TheJustMoose/74HCPU/hard/MUX1/MUX1.kicad_pcb

## KiCad design hard/MUX1/MUX1.kicad_pcb (2026-05-10)

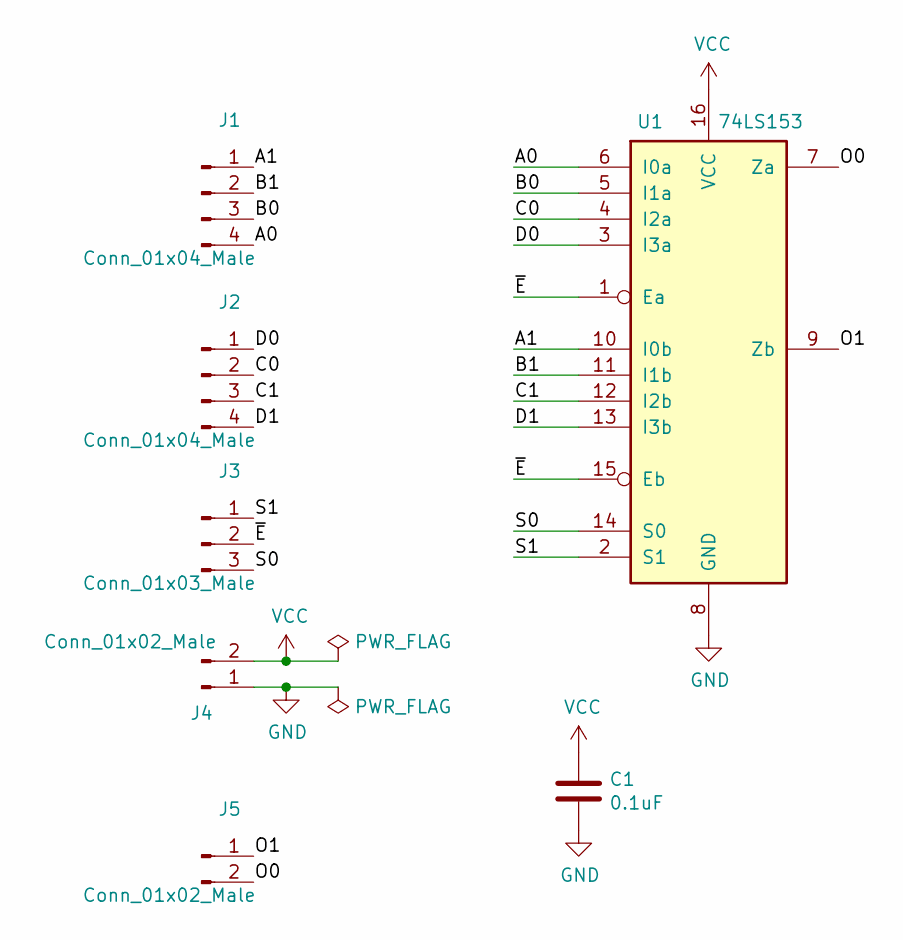
[picture p34: schematic MUX1.kicad_sch]

Parts:
C1: 0.1uF; C_0805_2012Metric_Pad1.18x1.45mm_HandSolder
J1, J2: Conn_01x04_Male; PinHeader_1x04_P2.54mm_Horizontal
J3: Conn_01x03_Male; PinHeader_1x03_P2.54mm_Horizontal
J4, J5: Conn_01x02_Male; PinHeader_1x02_P2.54mm_Horizontal
U1: 74LS153; SO-16_3.9x9.9mm_P1.27mm

Connections:
/A0: J1.4, U1.6 (I0a)
/A1: J1.1, U1.10 (I0b)
/B0: J1.3, U1.5 (I1a)
/B1: J1.2, U1.11 (I1b)
/C0: J2.2, U1.4 (I2a)
/C1: J2.3, U1.12 (I2b)
/D0: J2.1, U1.3 (I3a)
/D1: J2.4, U1.13 (I3b)
/O0: J5.2, U1.7 (Za)
/O1: J5.1, U1.9 (Zb)
/S0: J3.3, U1.14 (S0)
/S1: J3.1, U1.2 (S1)
/~E: J3.2, U1.1 (Ea), U1.15 (Eb)
GND: C1.2, J4.1, U1.8 (GND)
VCC: C1.1, J4.2, U1.16 (VCC)

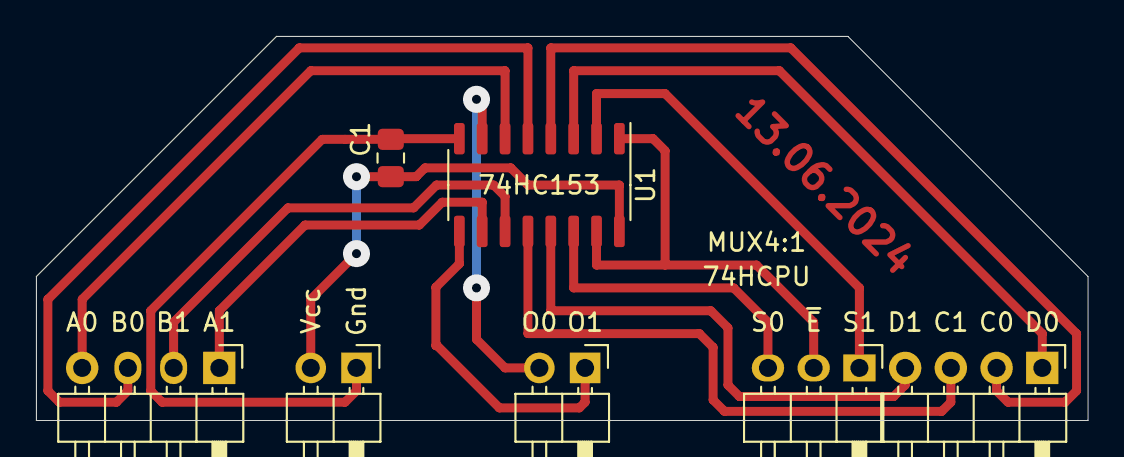
[picture p35: board MUX1.kicad_pcb from above]

Board: 2 copper layers, 58.4 x 21.3 mm, 7 parts (0 on the bottom side), 15 nets.
