TheJustMoose/74HCPU/hard/!ROM/ROM.kicad_pcb

## KiCad design hard/!ROM/ROM.kicad_pcb (2026-05-10)

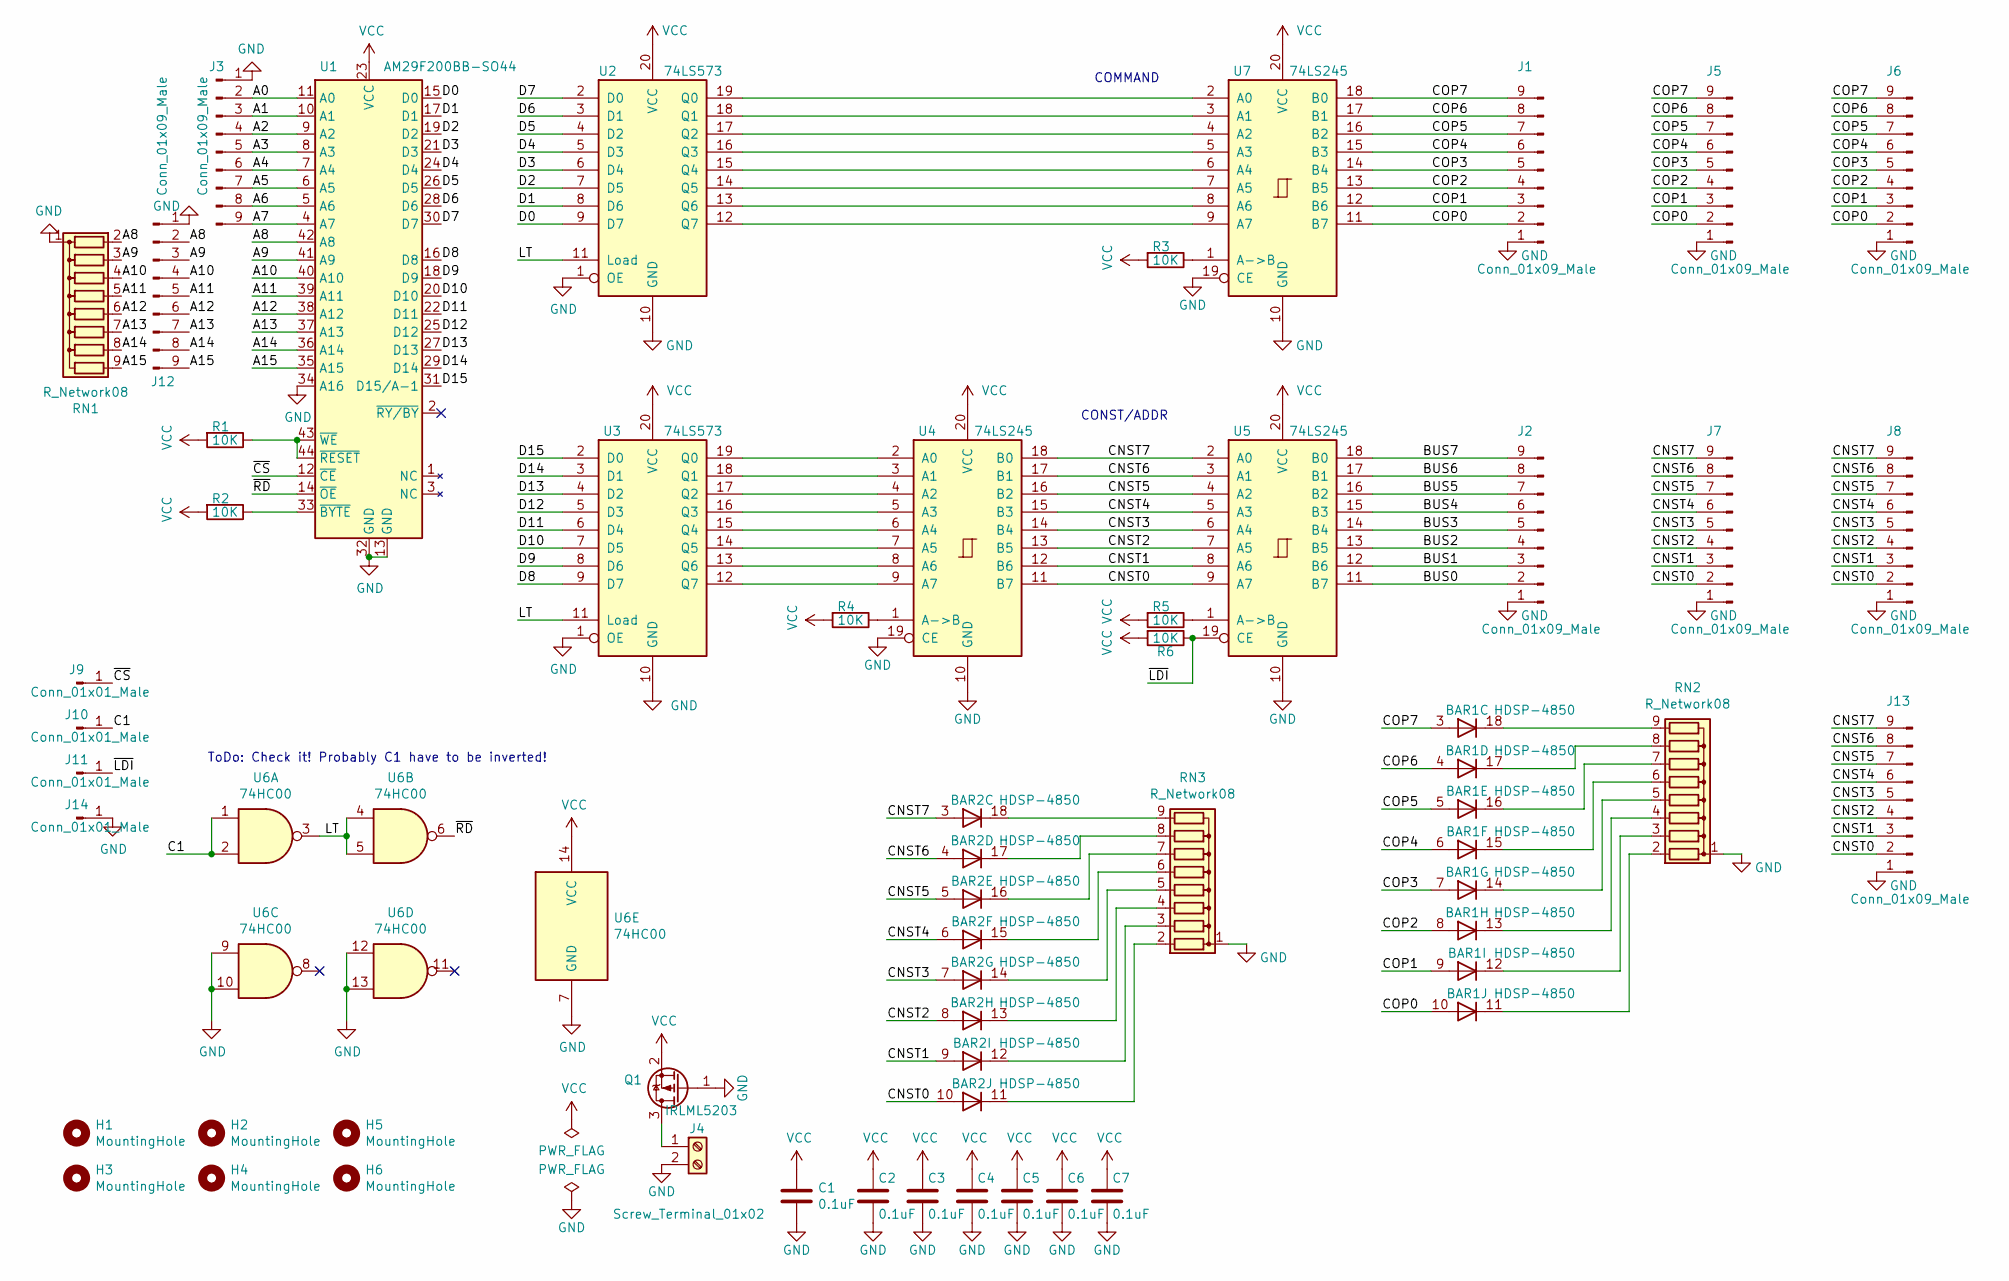
[picture p36: schematic ROM.kicad_sch]

Parts:
BAR1, BAR2: HDSP-4850
C1: 0.1uF; C_Rect_L24.0mm_W7.0mm_P22.50mm_MKT
C2, C3, C4, C5, C6, C7: 0.1uF; C_Disc_D7.5mm_W5.0mm_P7.50mm
H1, H2, H3, H4, H5, H6: MountingHole; MountingHole_3.2mm_M3
J1, J2, J3, J5, J6, J7, J8, J12, J13: Conn_01x09_Male; PinHeader_1x09_P2.54mm_Vertical
J4: Screw_Terminal_01x02; TerminalBlock_Phoenix_PT-1,5-2-5.0-H_1x02_P5.00mm_Horizontal
J9, J10, J11, J14: Conn_01x01_Male; PinHeader_1x01_P2.54mm_Vertical
Q1: IRLML5203; SOT-23
R1, R2, R3, R4, R5, R6: 10K; R_0805_2012Metric_Pad1.20x1.40mm_HandSolder
RN1, RN2, RN3: R_Network08; R_Array_SIP9
U1: AM29F200BB-SO44; DIP-44_W15.24mm
U2, U3: 74LS573; DIP-20_W7.62mm
U4, U5, U7: 74LS245; DIP-20_W7.62mm
U6: 74HC00; DIP-14_W7.62mm

Connections:
/A0: J3.2, U1.11 (A0)
/A1: J3.3, U1.10 (A1)
/A2: J3.4, U1.9 (A2)
/A3: J3.5, U1.8 (A3)
/A4: J3.6, U1.7 (A4)
/A5: J3.7, U1.6 (A5)
/A6: J3.8, U1.5 (A6)
/A7: J3.9, U1.4 (A7)
/A8: J12.2, RN1.2 (R1), U1.42 (A8)
/A9: J12.3, RN1.3 (R2), U1.41 (A9)
/A10: J12.4, RN1.4 (R3), U1.40 (A10)
/A11: J12.5, RN1.5 (R4), U1.39 (A11)
/A12: J12.6, RN1.6 (R5), U1.38 (A12)
/A13: J12.7, RN1.7 (R6), U1.37 (A13)
/A14: J12.8, RN1.8 (R7), U1.36 (A14)
/A15: J12.9, RN1.9 (R8), U1.35 (A15)
/BUS0: J2.2, U5.11 (B7)
/BUS1: J2.3, U5.12 (B6)
/BUS2: J2.4, U5.13 (B5)
/BUS3: J2.5, U5.14 (B4)
/BUS4: J2.6, U5.15 (B3)
/BUS5: J2.7, U5.16 (B2)
/BUS6: J2.8, U5.17 (B1)
/BUS7: J2.9, U5.18 (B0)
/C1: J10.1, U6.1, U6.2
/CNST0: BAR2.10 (A), J7.2, J8.2, J13.2, U4.11 (B7), U5.9 (A7)
/CNST1: BAR2.9 (A), J7.3, J8.3, J13.3, U4.12 (B6), U5.8 (A6)
/CNST2: BAR2.8 (A), J7.4, J8.4, J13.4, U4.13 (B5), U5.7 (A5)
/CNST3: BAR2.7 (A), J7.5, J8.5, J13.5, U4.14 (B4), U5.6 (A4)
/CNST4: BAR2.6 (A), J7.6, J8.6, J13.6, U4.15 (B3), U5.5 (A3)
/CNST5: BAR2.5 (A), J7.7, J8.7, J13.7, U4.16 (B2), U5.4 (A2)
/CNST6: BAR2.4 (A), J7.8, J8.8, J13.8, U4.17 (B1), U5.3 (A1)
/CNST7: BAR2.3 (A), J7.9, J8.9, J13.9, U4.18 (B0), U5.2 (A0)
/COP0: BAR1.10 (A), J1.2, J5.2, J6.2, U7.11 (B7)
/COP1: BAR1.9 (A), J1.3, J5.3, J6.3, U7.12 (B6)
/COP2: BAR1.8 (A), J1.4, J5.4, J6.4, U7.13 (B5)
/COP3: BAR1.7 (A), J1.5, J5.5, J6.5, U7.14 (B4)
/COP4: BAR1.6 (A), J1.6, J5.6, J6.6, U7.15 (B3)
/COP5: BAR1.5 (A), J1.7, J5.7, J6.7, U7.16 (B2)
/COP6: BAR1.4 (A), J1.8, J5.8, J6.8, U7.17 (B1)
/COP7: BAR1.3 (A), J1.9, J5.9, J6.9, U7.18 (B0)
/D0: U1.15 (D0), U2.9 (D7)
/D1: U1.17 (D1), U2.8 (D6)
/D2: U1.19 (D2), U2.7 (D5)
/D3: U1.21 (D3), U2.6 (D4)
/D4: U1.24 (D4), U2.5 (D3)
/D5: U1.26 (D5), U2.4 (D2)
/D6: U1.28 (D6), U2.3 (D1)
/D7: U1.30 (D7), U2.2 (D0)
/D8: U1.16 (D8), U3.9 (D7)
/D9: U1.18 (D9), U3.8 (D6)
/D10: U1.20 (D10), U3.7 (D5)
/D11: U1.22 (D11), U3.6 (D4)
/D12: U1.25 (D12), U3.5 (D3)
/D13: U1.27 (D13), U3.4 (D2)
/D14: U1.29 (D14), U3.3 (D1)
/D15: U1.31 (D15/A-1), U3.2 (D0)
/LT: U2.11 (Load), U3.11 (Load), U6.3, U6.4, U6.5
/~CS: J9.1, U1.12 (~CE)
/~LDI: J11.1, R6.1, U5.19 (CE)
/~RD: U1.14 (~OE), U6.6
GND: C1.2, C2.2, C3.2, C4.2, C5.2, C6.2, C7.2, J1.1, J2.1, J3.1, J4.2, J5.1, J6.1, J7.1, J8.1, J12.1, J13.1, J14.1, Q1.1 (G), RN1.1 (common), RN2.1 (common), RN3.1 (common), U1.13 (GND), U1.32 (GND), U1.34 (A16), U2.1 (OE), U2.10 (GND), U3.1 (OE), U3.10 (GND), U4.10 (GND), U4.19 (CE), U5.10 (GND), U6.7 (GND), U6.9, U6.10, U6.12, U6.13, U7.10 (GND), U7.19 (CE)
unnamed: BAR1.11 (K), RN2.2 (R1)
unnamed: BAR1.12 (K), RN2.3 (R2)
unnamed: BAR1.13 (K), RN2.4 (R3)
unnamed: BAR1.14 (K), RN2.5 (R4)
unnamed: BAR1.15 (K), RN2.6 (R5)
unnamed: BAR1.16 (K), RN2.7 (R6)
unnamed: BAR1.17 (K), RN2.8 (R7)
unnamed: BAR1.18 (K), RN2.9 (R8)
unnamed: BAR2.11 (K), RN3.2 (R1)
unnamed: BAR2.12 (K), RN3.3 (R2)
unnamed: BAR2.13 (K), RN3.4 (R3)
unnamed: BAR2.14 (K), RN3.5 (R4)
unnamed: BAR2.15 (K), RN3.6 (R5)
unnamed: BAR2.16 (K), RN3.7 (R6)
unnamed: BAR2.17 (K), RN3.8 (R7)
unnamed: BAR2.18 (K), RN3.9 (R8)
unnamed: J4.1, Q1.3 (D)
unnamed: R1.1, U1.43 (~WE), U1.44 (~RESET)
unnamed: R2.1, U1.33 (~BYTE)
unnamed: R3.1, U7.1 (A->B)
unnamed: R4.1, U4.1 (A->B)
unnamed: R5.1, U5.1 (A->B)
unnamed: U2.12 (Q7), U7.9 (A7)
unnamed: U2.13 (Q6), U7.8 (A6)
unnamed: U2.14 (Q5), U7.7 (A5)
unnamed: U2.15 (Q4), U7.6 (A4)
unnamed: U2.16 (Q3), U7.5 (A3)
unnamed: U2.17 (Q2), U7.4 (A2)
unnamed: U2.18 (Q1), U7.3 (A1)
unnamed: U2.19 (Q0), U7.2 (A0)
unnamed: U3.12 (Q7), U4.9 (A7)
unnamed: U3.13 (Q6), U4.8 (A6)
unnamed: U3.14 (Q5), U4.7 (A5)
unnamed: U3.15 (Q4), U4.6 (A4)
unnamed: U3.16 (Q3), U4.5 (A3)
unnamed: U3.17 (Q2), U4.4 (A2)
unnamed: U3.18 (Q1), U4.3 (A1)
unnamed: U3.19 (Q0), U4.2 (A0)
VCC: C1.1, C2.1, C3.1, C4.1, C5.1, C6.1, C7.1, Q1.2 (S), R1.2, R2.2, R3.2, R4.2, R5.2, R6.2, U1.23 (VCC), U2.20 (VCC), U3.20 (VCC), U4.20 (VCC), U5.20 (VCC), U6.14 (VCC), U7.20 (VCC)

Notes on the sheet:
CONST/ADDR
ToDo: Check it! Probably C1 have to be inverted!
COMMAND

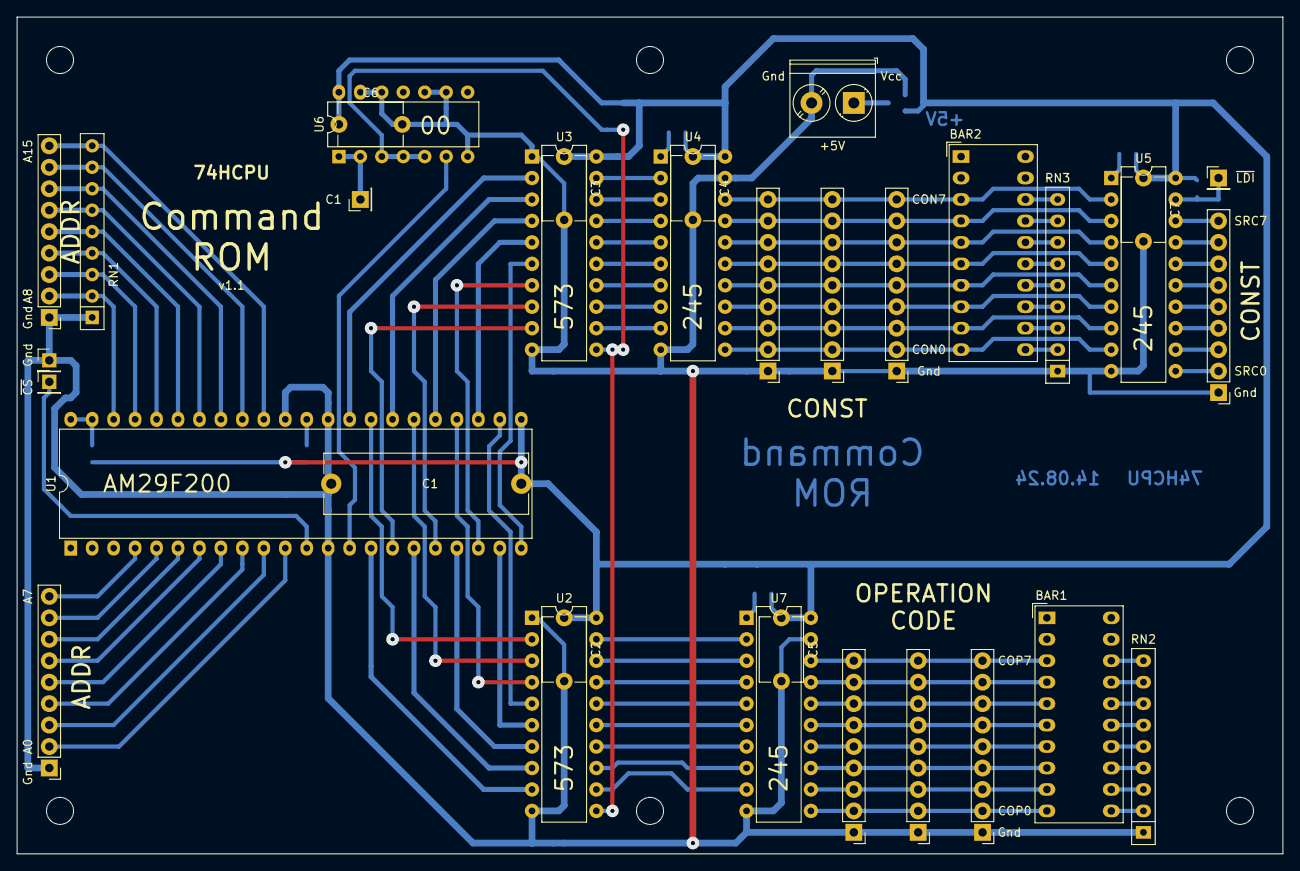
[picture p37: board ROM.kicad_pcb from above]

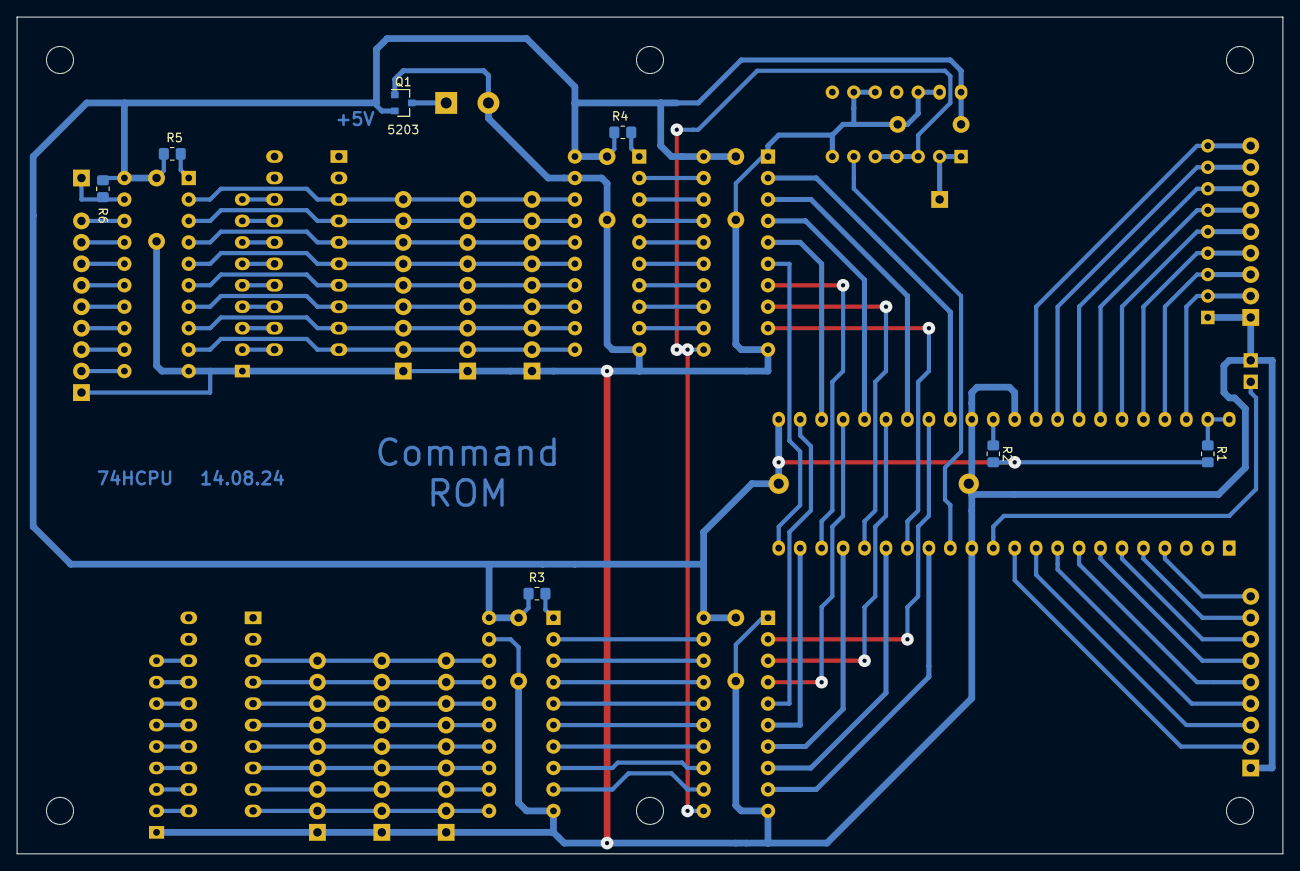
[picture p38: board ROM.kicad_pcb from below]

Board: 2 copper layers, 149.9 x 99.1 mm, 46 parts (7 on the bottom side), 101 nets.
