TheJustMoose/74HCPU/hard/!REGS/EndPlate/EndPlate.kicad_pcb

## KiCad design hard/!REGS/EndPlate/EndPlate.kicad_pcb (2026-05-01)

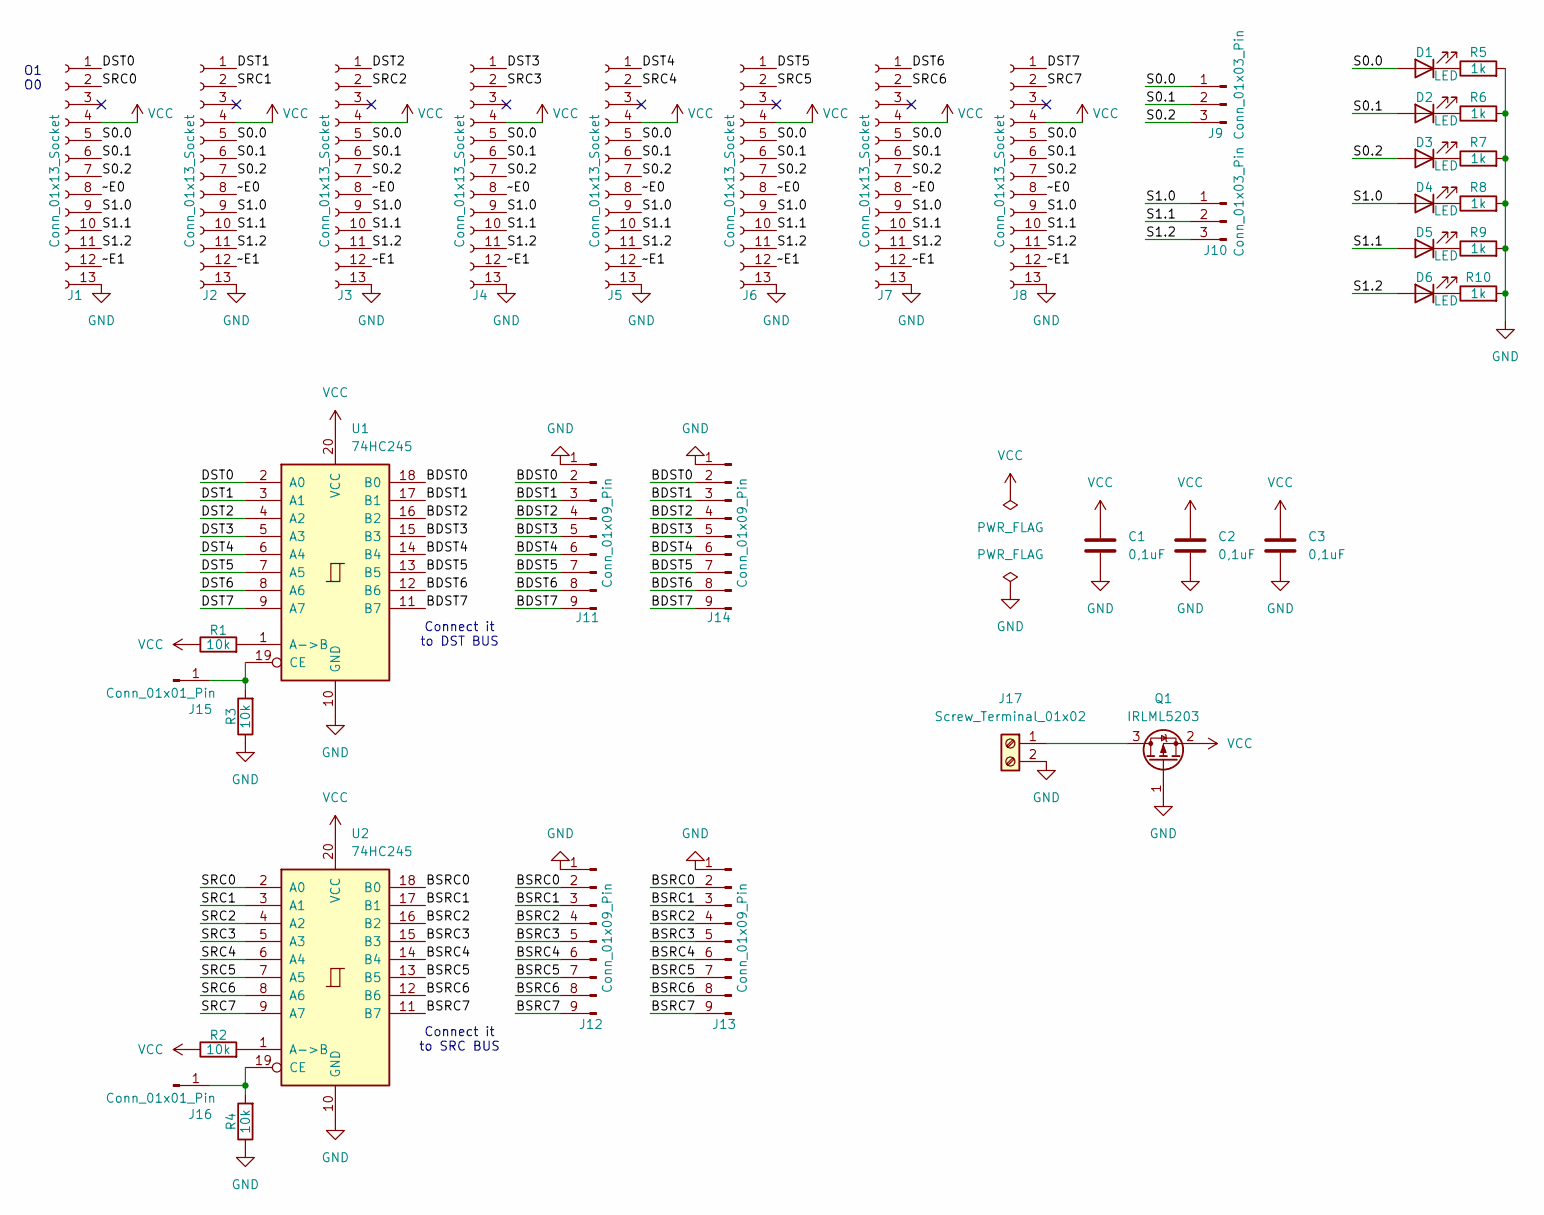
[picture p39: schematic EndPlate.kicad_sch]

Parts:
C1, C2: 0,1uF; C_Axial_L12.0mm_D6.5mm_P15.00mm_Horizontal
C3: 0,1uF; C_0805_2012Metric_Pad1.18x1.45mm_HandSolder
D1, D2, D3, D4, D5, D6: LED; LED_Rectangular_W5.0mm_H2.0mm
J1, J2, J3, J4, J5, J6, J7, J8: Conn_01x13_Socket; PinSocket_1x13_P2.54mm_Vertical_SMD_Pin1Left
J9, J10: Conn_01x03_Pin; PinHeader_1x03_P2.54mm_Vertical
J11, J12, J13, J14: Conn_01x09_Pin; PinHeader_1x09_P2.54mm_Vertical
J15, J16: Conn_01x01_Pin; PinHeader_1x01_P2.54mm_Vertical
J17: Screw_Terminal_01x02; TerminalBlock_Phoenix_MKDS-1,5-2_1x02_P5.00mm_Horizontal
Q1: IRLML5203; SOT-23
R1, R2, R3, R4: 10k; R_0805_2012Metric_Pad1.20x1.40mm_HandSolder
R5, R6, R7, R8, R9, R10: 1k; R_0805_2012Metric_Pad1.20x1.40mm_HandSolder
U1, U2: 74HC245; DIP-20_W7.62mm_Socket

Connections:
/BDST0: J11.2, J14.2, U1.18 (B0)
/BDST1: J11.3, J14.3, U1.17 (B1)
/BDST2: J11.4, J14.4, U1.16 (B2)
/BDST3: J11.5, J14.5, U1.15 (B3)
/BDST4: J11.6, J14.6, U1.14 (B4)
/BDST5: J11.7, J14.7, U1.13 (B5)
/BDST6: J11.8, J14.8, U1.12 (B6)
/BDST7: J11.9, J14.9, U1.11 (B7)
/BSRC0: J12.2, J13.2, U2.18 (B0)
/BSRC1: J12.3, J13.3, U2.17 (B1)
/BSRC2: J12.4, J13.4, U2.16 (B2)
/BSRC3: J12.5, J13.5, U2.15 (B3)
/BSRC4: J12.6, J13.6, U2.14 (B4)
/BSRC5: J12.7, J13.7, U2.13 (B5)
/BSRC6: J12.8, J13.8, U2.12 (B6)
/BSRC7: J12.9, J13.9, U2.11 (B7)
/DST0: J1.1, U1.2 (A0)
/DST1: J2.1, U1.3 (A1)
/DST2: J3.1, U1.4 (A2)
/DST3: J4.1, U1.5 (A3)
/DST4: J5.1, U1.6 (A4)
/DST5: J6.1, U1.7 (A5)
/DST6: J7.1, U1.8 (A6)
/DST7: J8.1, U1.9 (A7)
/S0.0: D1.2 (A), J1.5, J2.5, J3.5, J4.5, J5.5, J6.5, J7.5, J8.5, J9.1
/S0.1: D2.2 (A), J1.6, J2.6, J3.6, J4.6, J5.6, J6.6, J7.6, J8.6, J9.2
/S0.2: D3.2 (A), J1.7, J2.7, J3.7, J4.7, J5.7, J6.7, J7.7, J8.7, J9.3
/S1.0: D4.2 (A), J1.9, J2.9, J3.9, J4.9, J5.9, J6.9, J7.9, J8.9, J10.1
/S1.1: D5.2 (A), J1.10, J2.10, J3.10, J4.10, J5.10, J6.10, J7.10, J8.10, J10.2
/S1.2: D6.2 (A), J1.11, J2.11, J3.11, J4.11, J5.11, J6.11, J7.11, J8.11, J10.3
/SRC0: J1.2, U2.2 (A0)
/SRC1: J2.2, U2.3 (A1)
/SRC2: J3.2, U2.4 (A2)
/SRC3: J4.2, U2.5 (A3)
/SRC4: J5.2, U2.6 (A4)
/SRC5: J6.2, U2.7 (A5)
/SRC6: J7.2, U2.8 (A6)
/SRC7: J8.2, U2.9 (A7)
/~E0: J1.8, J2.8, J3.8, J4.8, J5.8, J6.8, J7.8, J8.8
/~E1: J1.12, J2.12, J3.12, J4.12, J5.12, J6.12, J7.12, J8.12
GND: C1.2, C2.2, C3.2, J1.13, J2.13, J3.13, J4.13, J5.13, J6.13, J7.13, J8.13, J11.1, J12.1, J13.1, J14.1, J17.2, Q1.1 (G), R3.1, R4.1, R5.2, R6.2, R7.2, R8.2, R9.2, R10.2, U1.10 (GND), U2.10 (GND)
unnamed: D1.1 (K), R5.1
unnamed: D2.1 (K), R6.1
unnamed: D3.1 (K), R7.1
unnamed: D4.1 (K), R8.1
unnamed: D5.1 (K), R9.1
unnamed: D6.1 (K), R10.1
unnamed: J15.1, R3.2, U1.19 (CE)
unnamed: J16.1, R4.2, U2.19 (CE)
unnamed: J17.1, Q1.3 (D)
unnamed: R1.2, U1.1 (A->B)
unnamed: R2.2, U2.1 (A->B)
VCC: C1.1, C2.1, C3.1, J1.4, J2.4, J3.4, J4.4, J5.4, J6.4, J7.4, J8.4, Q1.2 (S), R1.1, R2.1, U1.20 (VCC), U2.20 (VCC)

Notes on the sheet:
Connect it to DST BUS
Connect it to SRC BUS
O1 O0

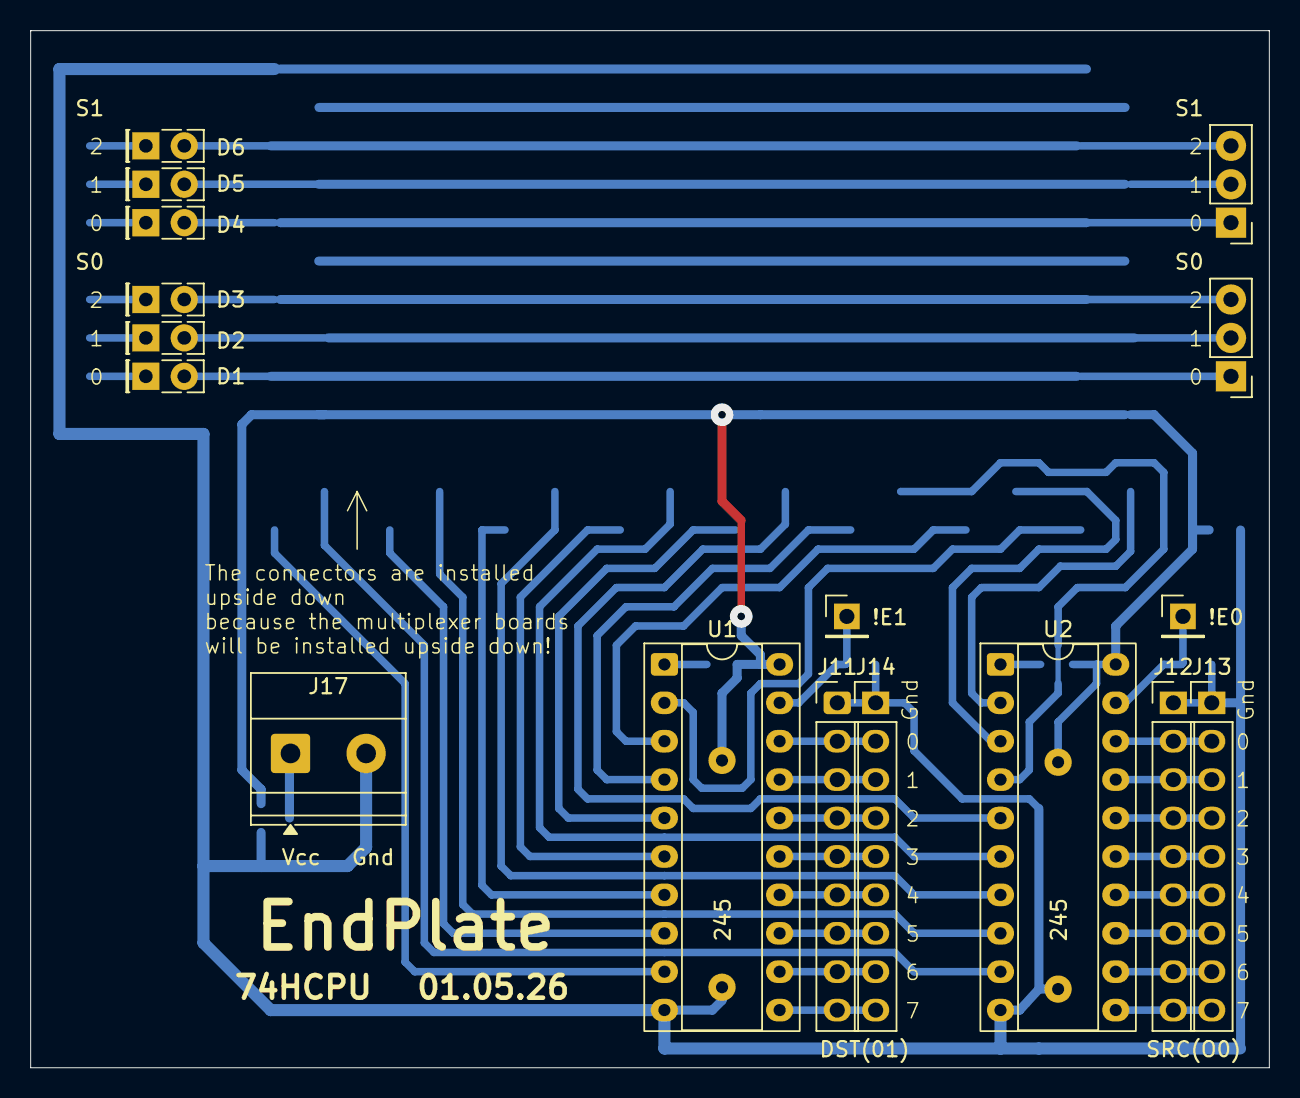
[picture p40: board EndPlate.kicad_pcb from above]

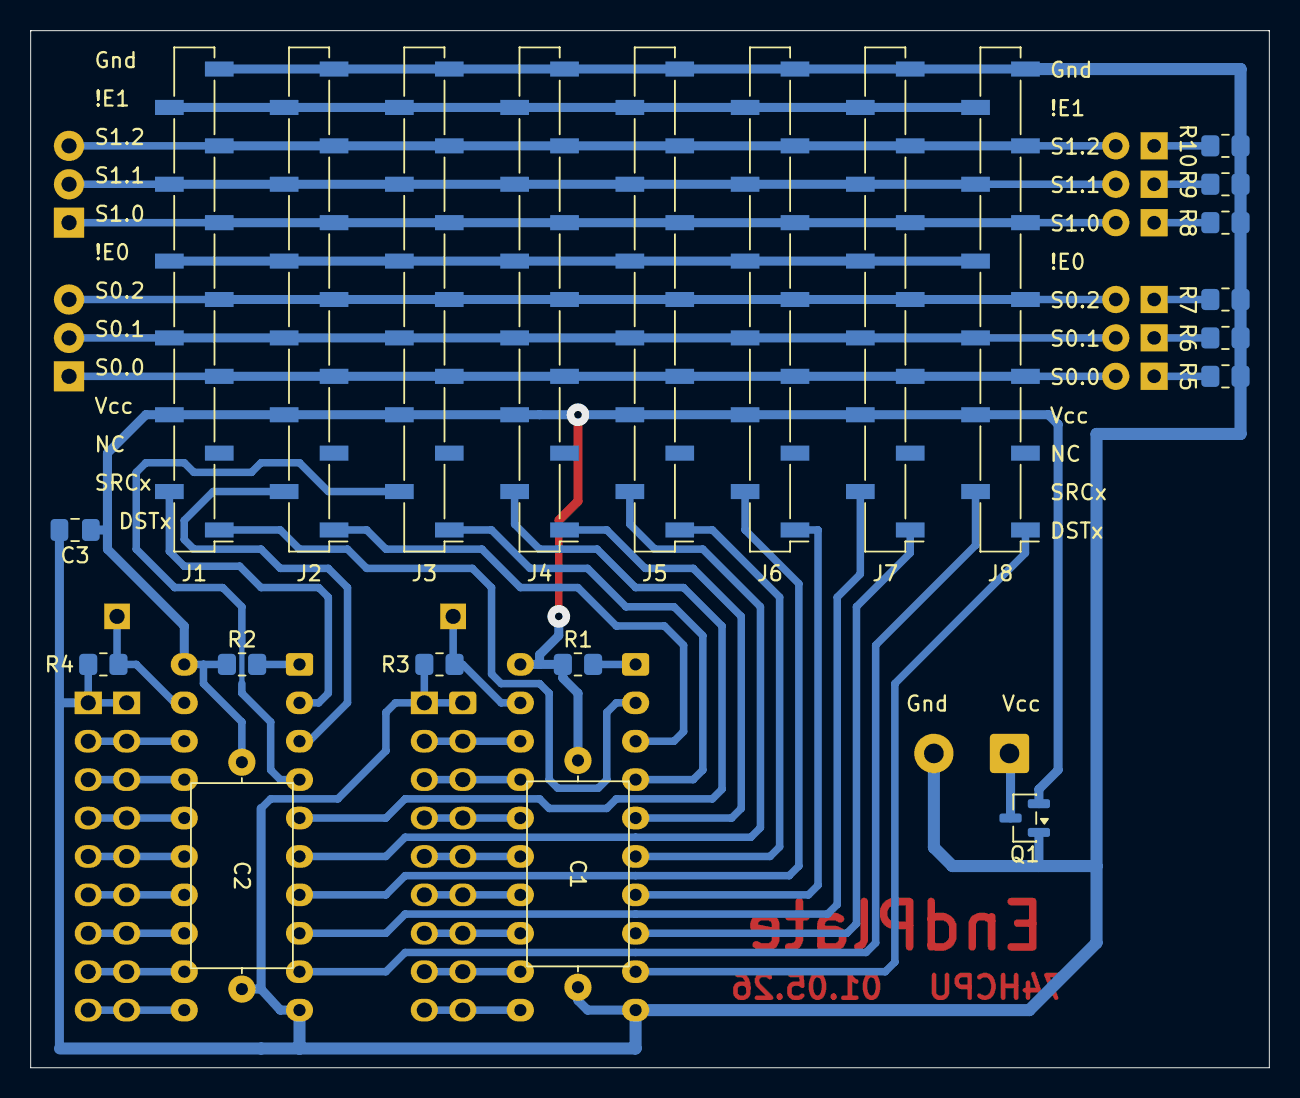
[picture p41: board EndPlate.kicad_pcb from below]

Board: 2 copper layers, 81.9 x 68.6 mm, 39 parts (22 on the bottom side), 53 nets.
