TheJustMoose/74HCPU/hard/!REGS/Regs-v5/Regs-v5.kicad_pcb

## KiCad design hard/!REGS/Regs-v5/Regs-v5.kicad_pcb (2026-03-27, an earlier design)

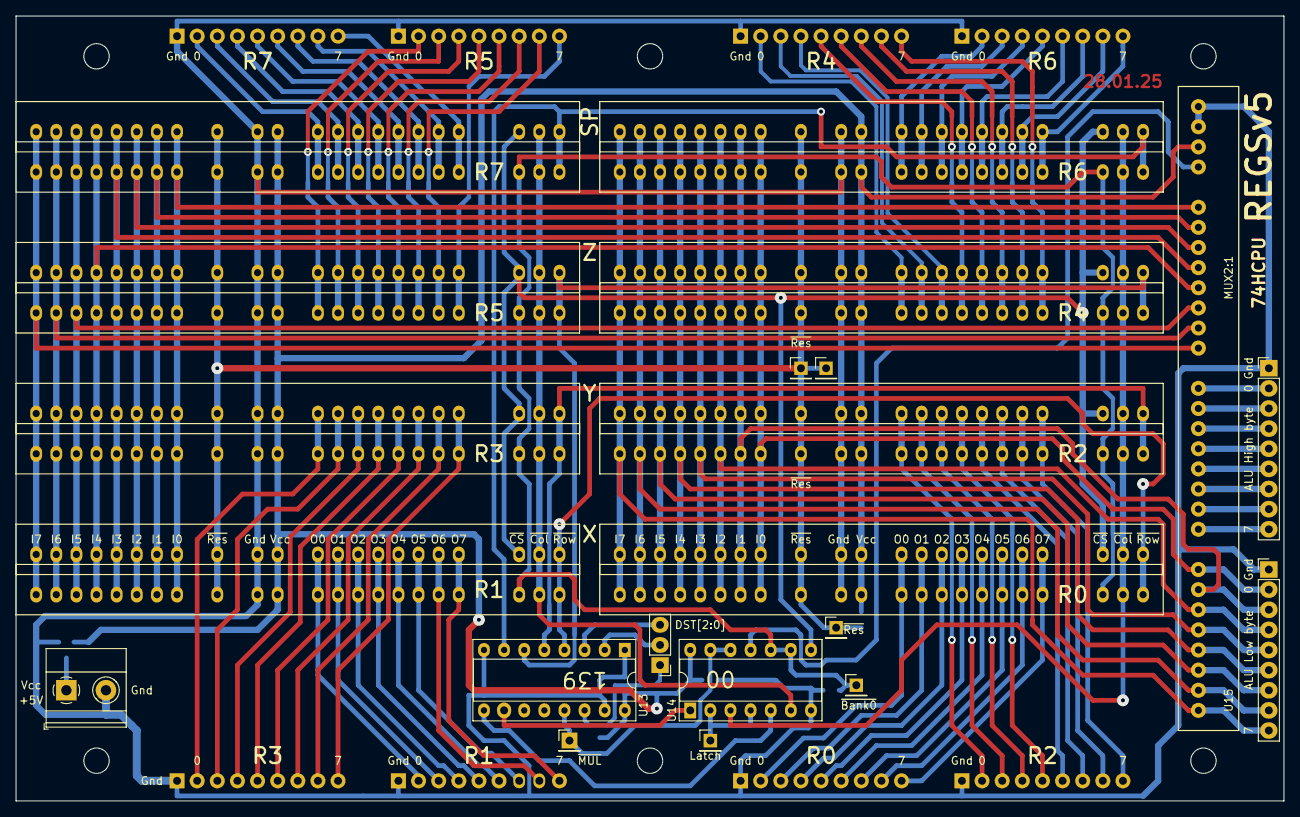
[picture p49: board Regs-v5.kicad_pcb from above]

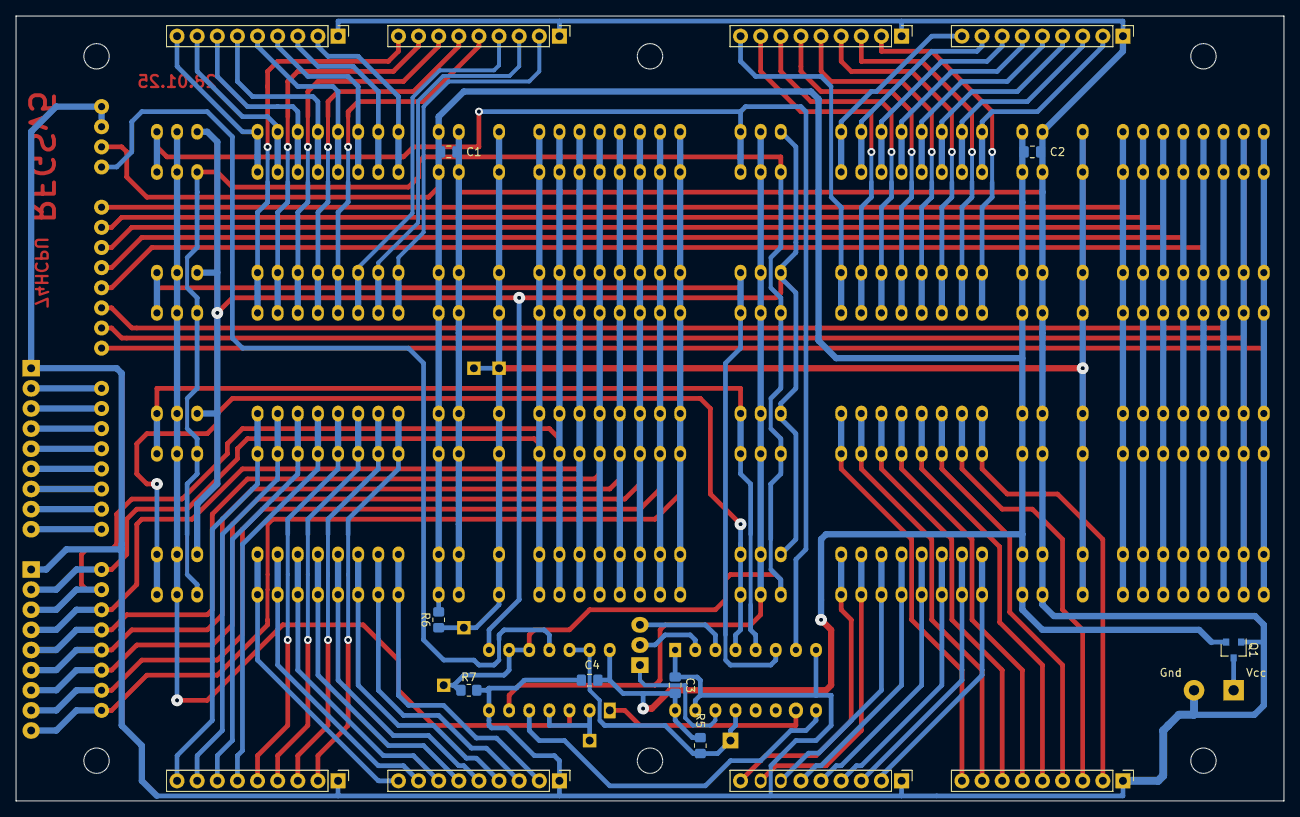
[picture p50: board Regs-v5.kicad_pcb from below]

Board: 2 copper layers, 160.0 x 99.1 mm, 51 parts (16 on the bottom side), 108 nets.

Parts:
C1, C2, C3, C4: 0.1uF; C_0805_2012Metric_Pad1.18x1.45mm_HandSolder
H1, H2, H3, H4, H5, H6: MountingHole; MountingHole_3.2mm_M3
J1, J2, J3, J4, J5, J6, J7, J8, J17, J18: Conn_01x09_Male; PinHeader_1x09_P2.54mm_Vertical
J11: Conn_01x03_Male; PinHeader_1x03_P2.54mm_Vertical
J12, J13, J14, J15, J19, J20: Conn_01x01_Male; PinHeader_1x01_P2.54mm_Vertical
J16: Screw_Terminal_01x02; TerminalBlock_Phoenix_MKDS-1,5-2_1x02_P5.00mm_Horizontal
Q1: IRLML5203; SOT-23
R5, R6, R7: 10k; R_0805_2012Metric_Pad1.20x1.40mm_HandSolder
U1, U2, U3, U4, U5, U6, U7, U8, U9, U10, U11, U12, U16, U17, U18, U19: REG_CNT
U13: 74LS139; DIP-16_W7.62mm_Socket
U14: 74HC00; DIP-14_W7.62mm_Socket
U15: MUX2-1; CMDwoC

Connections:
/ALU_H0: J18.2, U15.16
/ALU_H7: J18.9, U15.9
/DST[0]: J11.1, U13.14
/DST[1]: J11.2, U13.2
/DST[2]: J11.3, U13.3
/H0: U2.8, U4.8, U6.8, U8.8, U10.8, U12.8, U15.24, U17.8, U19.8
/H1: U2.7, U4.7, U6.7, U8.7, U10.7, U12.7, U15.23, U17.7, U19.7
/H2: U2.6, U4.6, U6.6, U8.6, U10.6, U12.6, U15.22, U17.6, U19.6
/H3: U2.5, U4.5, U6.5, U8.5, U10.5, U12.5, U15.21, U17.5, U19.5
/H4: U2.4, U4.4, U6.4, U8.4, U10.4, U12.4, U15.20, U17.4, U19.4
/H5: U2.3, U4.3, U6.3, U8.3, U10.3, U12.3, U15.19, U17.3, U19.3
/H6: U2.2, U4.2, U6.2, U8.2, U10.2, U12.2, U15.18, U17.2, U19.2
/H7: U2.1, U4.1, U6.1, U8.1, U10.1, U12.1, U15.17, U17.1, U19.1
/L0: J17.2, U1.8, U3.8, U5.8, U7.8, U9.8, U11.8, U15.8, U16.8, U18.8
/L1: J17.3, U1.7, U3.7, U5.7, U7.7, U9.7, U11.7, U15.7, U16.7, U18.7
/L2: J17.4, U1.6, U3.6, U5.6, U7.6, U9.6, U11.6, U15.6, U16.6, U18.6
/L3: J17.5, U1.5, U3.5, U5.5, U7.5, U9.5, U11.5, U15.5, U16.5, U18.5
/L4: J17.6, U1.4, U3.4, U5.4, U7.4, U9.4, U11.4, U15.4, U16.4, U18.4
/L5: J17.7, U1.3, U3.3, U5.3, U7.3, U9.3, U11.3, U15.3, U16.3, U18.3
/L6: J17.8, U1.2, U3.2, U5.2, U7.2, U9.2, U11.2, U15.2, U16.2, U18.2
/L7: J17.9, U1.1, U3.1, U5.1, U7.1, U9.1, U11.1, U15.1, U16.1, U18.1
/Latch: J15.1, U14.2, U14.4
/R0.0: J1.2, U1.12, U9.12
/R0.1: J1.3, U1.13, U9.13
/R0.2: J1.4, U1.14, U9.14
/R0.3: J1.5, U1.15, U9.15
/R0.4: J1.6, U1.16, U9.16
/R0.5: J1.7, U1.17, U9.17
/R0.6: J1.8, U1.18, U9.18
/R0.7: J1.9, U1.19, U9.19
/R1.0: J2.2, U2.12, U10.12
/R1.1: J2.3, U2.13, U10.13
/R1.2: J2.4, U2.14, U10.14
/R1.3: J2.5, U2.15, U10.15
/R1.4: J2.6, U2.16, U10.16
/R1.5: J2.7, U2.17, U10.17
/R1.6: J2.8, U2.18, U10.18
/R1.7: J2.9, U2.19, U10.19
/R2.0: J3.2, U3.12, U11.12
/R2.1: J3.3, U3.13, U11.13
/R2.2: J3.4, U3.14, U11.14
/R2.3: J3.5, U3.15, U11.15
/R2.4: J3.6, U3.16, U11.16
/R2.5: J3.7, U3.17, U11.17
/R2.6: J3.8, U3.18, U11.18
/R2.7: J3.9, U3.19, U11.19
/R3.0: J4.2, U4.12, U12.12
/R3.1: J4.3, U4.13, U12.13
/R3.2: J4.4, U4.14, U12.14
/R3.3: J4.5, U4.15, U12.15
/R3.4: J4.6, U4.16, U12.16
/R3.5: J4.7, U4.17, U12.17
/R3.6: J4.8, U4.18, U12.18
/R3.7: J4.9, U4.19, U12.19
/R4.0: J5.2, U5.12, U16.12
/R4.1: J5.3, U5.13, U16.13
/R4.2: J5.4, U5.14, U16.14
/R4.3: J5.5, U5.15, U16.15
/R4.4: J5.6, U5.16, U16.16
/R4.5: J5.7, U5.17, U16.17
/R4.6: J5.8, U5.18, U16.18
/R4.7: J5.9, U5.19, U16.19
/R5.0: J6.2, U6.12, U17.12
/R5.1: J6.3, U6.13, U17.13
/R5.2: J6.4, U6.14, U17.14
/R5.3: J6.5, U6.15, U17.15
/R5.4: J6.6, U6.16, U17.16
/R5.5: J6.7, U6.17, U17.17
/R5.6: J6.8, U6.18, U17.18
/R5.7: J6.9, U6.19, U17.19
/R6.0: J7.2, U7.12, U18.12
/R6.1: J7.3, U7.13, U18.13
/R6.2: J7.4, U7.14, U18.14
/R6.3: J7.5, U7.15, U18.15
/R6.4: J7.6, U7.16, U18.16
/R6.5: J7.7, U7.17, U18.17
/R6.6: J7.8, U7.18, U18.18
/R6.7: J7.9, U7.19, U18.19
/R7.0: J8.2, U8.12, U19.12
/R7.1: J8.3, U8.13, U19.13
/R7.2: J8.4, U8.14, U19.14
/R7.3: J8.5, U8.15, U19.15
/R7.4: J8.6, U8.16, U19.16
/R7.5: J8.7, U8.17, U19.17
/R7.6: J8.8, U8.18, U19.18
/R7.7: J8.9, U8.19, U19.19
/~Bank0: J14.1, R7.1, U1.20, U2.20, U3.20, U4.20, U5.20, U6.20, U7.20, U8.20, U14.9, U14.10
/~Bank1: U9.20, U10.20, U11.20, U12.20, U14.8, U16.20, U17.20, U18.20, U19.20
/~H: U2.21, U4.21, U6.21, U8.21, U10.21, U12.21, U14.6, U17.21, U19.21
/~L: U1.21, U3.21, U5.21, U7.21, U9.21, U11.21, U14.3, U16.21, U18.21
/~MUL: J12.1, R5.1, U13.13, U14.12, U14.13
/~R0: U1.22, U2.22, U9.22, U10.22, U13.4
/~R1: U3.22, U4.22, U11.22, U12.22, U13.5
/~R2: U5.22, U6.22, U13.6, U16.22, U17.22
/~R3: U7.22, U8.22, U13.7, U18.22, U19.22
/~Res: J13.1, J19.1, J20.1, R6.1, U1.9, U2.9, U3.9, U4.9, U5.9, U6.9, U7.9, U8.9, U9.9, U10.9, U11.9, U12.9, U16.9, U17.9, U18.9, U19.9
GND: C1.2, C2.2, C3.2, C4.2, J1.1, J2.1, J3.1, J4.1, J5.1, J6.1, J7.1, J8.1, J16.2, J17.1, J18.1, Q1.1, R7.2, U1.10, U2.10, U3.10, U4.10, U5.10, U6.10, U7.10, U8.10, U9.10, U10.10, U11.10, U12.10, U13.1, U13.8, U13.15, U14.7, U15.27, U15.28, U16.10, U17.10, U18.10, U19.10
unnamed: J16.1, Q1.3
unnamed: J18.3, U15.15
unnamed: J18.4, U15.14
unnamed: J18.5, U15.13
unnamed: J18.6, U15.12
unnamed: J18.7, U15.11
unnamed: J18.8, U15.10
unnamed: U13.9, U14.5
unnamed: U13.10, U14.1
unnamed: U14.11, U15.25
VCC: C1.1, C2.1, C3.1, C4.1, Q1.2, R5.2, R6.2, U1.11, U2.11, U3.11, U4.11, U5.11, U6.11, U7.11, U8.11, U9.11, U10.11, U11.11, U12.11, U13.16, U14.14, U15.26, U16.11, U17.11, U18.11, U19.11
