TheJustMoose/74HCPU/soft/expr/backend.cc

#include "backend.h"
#include "var_list.h"
#include "parser.h"
#include "regs_bank.h"
#include "spillable.h"
#include "var.h"
#include "var_list.h"
#include "var_size.h"

#include <algorithm>
#include <iostream>
#include <string>
#include <sstream>

using namespace std;

/*

 Добавить юнит тестов для уже написанных Spill / Fill.
 Сделать какой-то синглтон, из которого торчат переменные, адреса, и степень их заспиленности!
 Как-то переделать табличку со списком Operation

*/

// copied from asm
string ToUpper(string s) {
  transform(s.begin(), s.end(), s.begin(), ::toupper);
  return s;
}

string AlignNumber(string s, int width) {
  string res {s};
  while (res.size() < width)
    res = "0" + res;
  return res;
}

string AlignByWidth(string s, int width, char c = ' ') {
  string res {s};
  string fll({c});
  while (res.size() < width)
    res += fll;
  return res;
}

string ToHexString(int value, int width = 4) {
  stringstream ss;
  ss << hex << value;
  return AlignNumber(ToUpper(ss.str()), width);
}

class RegSpillable: public ISpillable {
 public:
  RegSpillable(Backend* backend, map<string, uint16_t> var_addrs)
    : backend_(backend), var_addrs_(var_addrs) {}

  void Spill(size_t reg_idx, uint16_t var_addr,
             string var_name) override;

  void Fill(string var_name, string reg_name) override;

 private:
  Backend* backend_ {nullptr};
  map<string, uint16_t> var_addrs_;
};

void RegSpillable::Spill(size_t reg_idx, uint16_t var_addr,
                         string var_name) {
  cout << "// No free registers. Will spill R" << reg_idx
       << " with " << var_name
       << " to addr " << var_addr << endl;

  if (!backend_) {
    cout << "backend_ is NULL" << endl;
    return;
  }

  backend_->SwitchToBank1();
  backend_->AddAsmInstruction(string("mov XL, 0x") + ToHexString(var_addr & 0xFF));
  backend_->AddAsmInstruction(string("mov XH, 0x") + ToHexString((var_addr >> 8) & 0xFF));
  backend_->SwitchToBank0();
  backend_->AddAsmInstruction(string("st X, R") + to_string(reg_idx), var_name);
}

void RegSpillable::Fill(string var_name, string reg_name) {
  // Okay, we already know that var_name was spilled early...
  if (var_addrs_.find(var_name) == var_addrs_.end()) {
    cout << "Error. Address of variable " << var_name << "was not found" << endl;
    return;
  }

  uint16_t var_addr = var_addrs_[var_name];

  backend_->SwitchToBank1();
  backend_->AddAsmInstruction(string("mov XL, 0x") + ToHexString(var_addr & 0xFF));
  backend_->AddAsmInstruction(string("mov XH, 0x") + ToHexString((var_addr >> 8) & 0xFF));
  backend_->SwitchToBank0();
  backend_->AddAsmInstruction(string("ld ") + reg_name + string(", X"), var_name);
}

size_t reg_cnt = 8;
vector<string> bank1(reg_cnt);

string FindPtrFor(string var_name) {
  // check existing pair ptr:reg
  if (bank1[0] == var_name)
    return "X";
  if (bank1[2] == var_name)
    return "Y";

  // try to insert new pair ptr:reg
  if (!bank1[0].size()) {
    bank1[0] = var_name;
    return "X";
  } else if (!bank1[2].size()) {
    bank1[2] = var_name;
    return "Y";
  } else {
  }

  // oops
  return "";
}

void Backend::AddAsmInstruction(string instr, string cmnt, string cmnt2) {
  string res {instr};
  if (cmnt.size()) {
    res = AlignByWidth(res, 22);
    res += "// ";
    res += AlignByWidth(cmnt, 10);
    res += cmnt2;
  }
  res_asm_.push_back(res);
}

void Backend::SwitchToBank0() {
  AddAsmInstruction("out  CPU_FLAGS, 0", "switch to bank 0");
}

void Backend::SwitchToBank1() {
  AddAsmInstruction("out  CPU_FLAGS, 0x40", "switch to bank 1");
}

void Backend::FreeTheRegisters(RegsBank0& bank0, const Operation& op) {
  size_t var_cnt = op.live_out_vars.size();  // this variables are still alive after instruction
  for (size_t i = 0; i < var_cnt; i++) {
    if (op.live_in_vars[i] && !op.live_out_vars[i]) {  // var has died
      string reg_name = idx_to_var_[i];
      size_t idx = bank0.GetIndexOfVar(reg_name);
      cout << "variable with idx == " << i
           << ", var_name: " << bank0[idx] << " has died" << endl;
      cout << "reg_name: " << reg_name << ", reg_idx: " << idx << endl;
      bank0.FreeTheRegister(idx);
      cout << bank0.DumpRegs() << endl;
    }
  }
}

void Backend::GenerateAssignment(RegsBank0& bank0, Operation op, Var& v) {
  if (v.is_ptr) {  // pointer ops
    string lval;
    string hval;
    if (op.num_pos() == npLeft) {  // pointer1 = 0x1000
      int val = std::stoi(op.left_arg);
      lval = ToHexString(val & 0xFF, 3) + "h";
      hval = ToHexString((val >> 8) & 0xFF, 3) + "h";
    } else {  // pointer1 = pointer2
      string left = FindPtrFor(op.left_arg);
      lval = left + "L";
      hval = left + "H";
    }

    string cmnt1 = op.res_arg + " = " + op.left_arg;

    string res_reg = FindPtrFor(op.res_arg);
    SwitchToBank1();
    string line1 = "mov " + res_reg + "L, " + lval;
    AddAsmInstruction(line1, cmnt1);
    string line2 = "mov " + res_reg + "H, " + hval;
    AddAsmInstruction(line2);
    SwitchToBank0();
  } else {  // ordinary regs
    string cmnt1 = op.res_arg + " = " + op.left_arg;

    string res_reg = bank0.FindRegFor(op.res_arg);
    string right_val = (op.num_pos() == npLeft) ? op.left_arg : bank0.FindRegFor(op.left_arg);
    string line1 = "mov " + res_reg + ", " + right_val;
    AddAsmInstruction(line1, cmnt1, bank0.DumpRegs());
  }
}

void Backend::GenerateInvertion(RegsBank0& bank0, Operation op) {
  string cmnt1 = op.res_arg + " = " + op.op_name + op.right_arg;
  string res_reg = bank0.FindRegFor(op.res_arg);
  if (op.num_pos() == npRight) {  // c = -3
    string line1 = "mov " + res_reg + ", " + op.op_name + op.right_arg;
    AddAsmInstruction(line1, cmnt1);
  } else {  // R0 = -R1
    // mov R0, ~R1; add R0, 1        // v1
    // xor R0, R0; addc R0, ~R1 + 1  // v2
    string line1 = "mov " + res_reg + ", ~" + bank0.FindRegFor(op.right_arg);
    AddAsmInstruction(line1, cmnt1);
    string line2 = "add " + res_reg + ", 1";
    AddAsmInstruction(line2);
  }
}

void Backend::GenerateBinOps(RegsBank0& bank0, Operation op) {
  // c = a + b   -->   c = a, c += b
  // what about var_size ?
  string cmnt1 = op.res_arg + " = " + op.left_arg;  // c = a

  string res_reg = bank0.FindRegFor(op.res_arg);
  string line1 = "mov " + res_reg + ", " + bank0.FindRegFor(op.left_arg);
  AddAsmInstruction(line1, cmnt1, bank0.DumpRegs());

  string cmnt2 = op.res_arg + " " + op.op_name + "= " + op.right_arg;  // c += b

  string cmd;
  if (op.op_name == "+")
    cmd = "add";
  else if (op.op_name == "-")
    cmd = "sub";
  else if (op.op_name == "*")
    cmd = "mul";
  else if (op.op_name == "/")
    cmd = "/ - not implemented!";
  else
    cmd = "unk";

  string right_val = (op.num_pos() == npRight) ? op.right_arg : bank0.FindRegFor(op.right_arg);
  string line2 = cmd + " " + res_reg + ", " + right_val;
  AddAsmInstruction(line2, cmnt2, bank0.DumpRegs());
}

void Backend::GenerateRelOps(RegsBank0& bank0, Operation op) {
  // c = a > b
  string cmnt1 = op.res_arg + " = " + op.left_arg + " " + op.op_name + " " + op.right_arg;

  string cmd;
  if (op.op_name == "<")
    cmd = "cmp";
  else if (op.op_name == ">")
    cmd = "cmp";
  else
    cmd = "unk";

  string left_reg = bank0.FindRegFor(op.left_arg);
  string right_val = (op.num_pos() == npRight) ? op.right_arg : bank0.FindRegFor(op.right_arg);
  string line1 = cmd + " " + left_reg + ", " + right_val;
  AddAsmInstruction(line1, cmnt1, bank0.DumpRegs());
}

void Backend::GenerateLabel(RegsBank0& bank0, Operation op) {
  string line1 = op.res_arg + ":";
  AddAsmInstruction(line1);
}

void Backend::GenerateJmp(RegsBank0& bank0, Operation op) {
  string line1 = op.res_arg + " " + op.left_arg;
  AddAsmInstruction(line1);
}

void Backend::GenerateBranch(RegsBank0& bank0, Operation op) {
  string line1 = op.res_arg + " " + op.left_arg;
  AddAsmInstruction(line1);
}

void Backend::GenerateCode(vector<Operation> code) {
  RegSpillable reg_spillable(this, var_addrs_);
  RegsBank0 bank0(&reg_spillable, var_addrs_, res_asm_);

  res_asm_.clear();

  for (Operation op : code) {
    if (op.op_type() == otBinaryArithm) {  // arithm ops (left_arg is not empty)
      GenerateBinOps(bank0, op);
    } else if (op.op_type() == otUnaryArithm) {  // assign ops (t1 = -t1)
      GenerateInvertion(bank0, op);
    } else if (op.op_type() == otRelational) {
      GenerateRelOps(bank0, op);
    } else if (op.op_type() == otAssignment) {  // empty op_name means assignment
      Var v;
      if (!getVar(op.res_arg, v)) {
        cout << "Variable " << op.res_arg << " was not declared" << endl;
        continue;
      }
      GenerateAssignment(bank0, op, v);
    } else if (op.op_type() == otLabel) {
      GenerateLabel(bank0, op);
    } else if (op.op_type() == otJmp) {
      GenerateJmp(bank0, op);
    } else if (op.op_type() == otBranch) {
      GenerateBranch(bank0, op);
    } else {
      cout << "**** FIXME! ****" << endl;
      cout << "Unknown op type: " << (int)op.op_type() << endl;
    }

    FreeTheRegisters(bank0, op);
  }
}
