TheJustMoose/74HCPU/soft/expr/compile.cpp

#include "compile.h"
#include "backend.h"
#include "func_guard.h"
#include "lexer.h"
#include "node.h"
#include "nodes.h"
#include "optimize.h"
#include "parser.h"
#include "print_tree.h"
#include "var_list.h"
#include "visitor.h"

#include <cstdint>
#include <iostream>
#include <map>
#include <memory>
#include <vector>

using namespace std;

int label_counter {0};
string new_label() {
  return to_string(label_counter++);
}

string RelationalOp2Branch(string op) {
  if (op == "<")
    return "jl";
  if (op == ">")
    return "jg";
  return "unk_br";
}

void PrintTableHeader() {
  cout << "|   res   | = |   left  |    op   |  right  |   numIn  |  optype  |" << endl;
}

void Print(const vector<Operation>& res_code) {
  PrintTableHeader();
  for (const Operation& r : res_code)
    cout << r.raw() << endl;
}

void PrintIR(const vector<Operation>& res_code) {
  for (const Operation& n : res_code) {
    uint8_t sz {0};
    if (isDeclared(n.res_arg, &sz))
      cout << n.str() << "(size: " << static_cast<int>(sz) << ")" << endl;
    else if (n.res_in_temp)
      cout << n.str() << endl;
    else
      cout << n.str() << "  // was not declared" << endl;
  }
}

void PrintLiveVars(const vector<Operation>& res_code,
                   map<size_t, string> idx_to_var) {
  PrintTableHeader();
  for (const Operation& r : res_code) {
    cout << r.raw() << endl;
    cout << r.live_vars_str(idx_to_var) << endl;
  }
}

class DataTypesSetter: public Visitor {
 public:
  void Visit(Name* nm_node) override {
    if (!nm_node)
      return;

    Var v;
    if (getVar(nm_node->name(), v))
      nm_node->init_data_type(v.data_type);
  }
};

void SetDataTypes(Node* root) {
  DataTypesSetter dts;
  root->accept(&dts);
}

class VarsCollector: public Visitor {
 public:
  void Visit(BinOp* binop_node) override {
    if (!binop_node)
      return;
    AddVar(binop_node->name(), binop_node->data_type(), false);  // is_ptr ?
  }

  void Visit(UnMinus* unop_node) override {
    if (!unop_node)
      return;
    AddVar(unop_node->name(), unop_node->data_type(), false);  // can we set is_ptr to true when argument is pointer?
  }
};

void CollectTempVars(Node* root) {
  VarsCollector vc;
  root->accept(&vc);
}

class CodeCollector: public Visitor {
 public:
  CodeCollector(vector<Operation>& a_res_code)
    : res_code(a_res_code) {}

  void Visit(AssignOp* asop_node) override {
    if (!asop_node->left) {
      cout << FuncGuard::stack_str() << "left == nullptr" << endl;
      return;
    }

    Name* name_node = dynamic_cast<Name*>(asop_node->left.get());
    if (!name_node) {
      cout << FuncGuard::stack_str() << "Error. left node is not variable (Name class)" << endl;
      return;
    }

    cout << FuncGuard::stack_str()
         << name_node->name() << " = "
         << asop_node->right->name() << endl;

    res_code.emplace_back(name_node->name(), "", asop_node->right->name(),
                          asop_node->get_num_pos(), "", otAssignment);
  }

  void Visit(BinOp* binop_node) override {
    if (!binop_node->left)
      cout << "left node is nullptr" << endl;
    else if (!binop_node->right)
      cout << "right node is nullptr" << endl;
    else {
      // Okay, let's put operation result into temp variable
      cout << FuncGuard::stack_str() << binop_node->name() << " = "
           << binop_node->left->name() << " " << binop_node->op() << " "
           << binop_node->right->name() << endl;
    }

    res_code.emplace_back(binop_node->name(), binop_node->op(), binop_node->left->name(),
                          binop_node->get_num_pos(), binop_node->right->name(), otBinaryArithm, true);
  }

  /*
      if (a > b) {
          c = 1;
      } else {
          c = 2;
      }
      d = c + 5;

      cmp a, b           // сравнить a и b
      jle L_else         // если a <= b, перейти в else
      c = 1
      goto L_end
  L_else:
      c = 2
  L_end:
      d = c + 5
  */
  void Visit(IfStatement* if_node) override {
    cout << "Visit(IfStatement*)" << endl;
    if (!if_node->then_body)
      cout << "then_body node is nullptr" << endl;
    else if (!if_node->cond)
      cout << "condition node is nullptr" << endl;
    else if (RelationalOp* rop = dynamic_cast<RelationalOp*>(if_node->cond.get())) {
        if_node->cond->accept(this);

        string end_label = "endif" + new_label();
        string then_label = "then" + new_label();
        string else_label = "else" + new_label();

        string br = RelationalOp2Branch(rop->op());
        res_code.emplace_back(br, "", then_label,
                              npNone, "", otBranch);

        res_code.emplace_back(else_label, "", "",
                              npNone, "", otLabel);
        if (if_node->else_body)
          if_node->else_body->accept(this);
        res_code.emplace_back("jmp", "", end_label,
                              npNone, "", otJmp);
        res_code.emplace_back(then_label, "", "",
                              npNone, "", otLabel);
        if (if_node->then_body)
          if_node->then_body->accept(this);
        res_code.emplace_back(end_label, "", "",
                              npNone, "", otLabel);
    } else {
        cout << "IfStatement require RelationalOp as a condition" << endl;
    }
  }

  void Visit(Name*) override {
    // name value will be used by other nodes
  }

  void Visit(Node*) override {
  }

  void Visit(RelationalOp* relop_node) {
    if (!relop_node->left)
      cout << "left node is nullptr" << endl;
    else if (!relop_node->right)
      cout << "right node is nullptr" << endl;
    else {
      res_code.emplace_back(relop_node->name(), relop_node->op(), relop_node->left->name(),
                            relop_node->get_num_pos(), relop_node->right->name(), otRelational, true);
    }
  }

  void Visit(UnMinus* unop_node) override {
    // the negative value is stored in the tree in two nodes: ntUMinus + ntNum
    cout << FuncGuard::stack_str() << unop_node->name() << " = "
         << unop_node->op() << unop_node->child->name() << " " << endl;

    res_code.emplace_back(unop_node->name(), unop_node->op(), "",
                          unop_node->get_num_pos(), unop_node->child->name(), otUnaryArithm, true);
  }

  void Visit(VarDecl* vd_node) override {
    for (string n : vd_node->names)
      if (vd_node->values.find(n) != vd_node->values.end())
        res_code.emplace_back(n, "", to_string(vd_node->values[n]), npLeft, "", otAssignment);
  }

 private:
  vector<Operation>& res_code;
};

void CollectCode(Node* root, vector<Operation>& res_code) {
  CodeCollector cc(res_code);
  root->accept(&cc);
}

int Compile(string code) {
  FuncGuard fg("compile");

  Lexer::instance().setInputString(code);

  vector<unique_ptr<Node>> statements;
  if (!program(statements))
    return 1;

  for (size_t i = 0; i < statements.size(); i++) {
    VarDecl* decl_node = dynamic_cast<VarDecl*>(statements[i].get());
    if (!decl_node)
      continue;

    for (string var_name : decl_node->names) {
      AddVar(var_name, decl_node->data_type(), decl_node->is_pointer());
      cout << GetDataTypeName(decl_node->data_type())
           << " variable \"" << var_name
           << (decl_node->is_pointer() ? "@" : "")
           << "\" has been declared" << endl;
    }
  }

  for (size_t i = 0; i < statements.size(); i++)
    SetDataTypes(statements[i].get());

  for (size_t i = 0; i < statements.size(); i++)
    CollectTempVars(statements[i].get());

  map<string, uint16_t> var_addrs;
  map<string, size_t> var_idxs;
  map<size_t, string> idx_to_var;

  cout << "decls:" << endl;
  uint16_t addr {0};
  cout << "| var | data_type | addr |" << endl;
  for (size_t i = 0; i < getVarCount(); i++) {
    Var v = getVar(i);
    cout << "| " << v.name << " | "
         << GetDataTypeName(v.data_type) << (v.is_ptr ? "@" : "")
         << " | " << addr << " | " << endl;

    var_addrs[v.name] = addr;  // var name -> var addr
    var_idxs[v.name] = i;      // index of variable inside of parser
    idx_to_var[i] = v.name;    // GetVar duplicate
    addr += v.size();
  }

  cout << "nodes:" << endl;
  vector<Operation> res_code;
  for (size_t i = 0; i < statements.size(); i++)
    if (statements[i])  // enum tree items, generate three-address code
      CollectCode(statements[i].get(), res_code);
    else
      cout << "statements[i] is null" << endl;

  cout << "res_code.size(): " << res_code.size() << endl << endl;

  for (size_t i = 0; i < statements.size(); i++)
    if (statements[i])
      PrintTree(statements[i].get());

  Print(res_code);
  cout << endl;

  cout << "try to optimize:" << endl;
  Optimize(res_code);
  cout << "res_code.size(): " << res_code.size() << endl;

  Print(res_code);

  cout << endl << "final IR:" << endl;
  PrintIR(res_code);

  cout << endl << "vars:" << endl;
  printVars();

  cout << endl << "processing live&dead vars..." << endl;
  vector<bool> live_vars(var_idxs.size(), false);
  for (int i = res_code.size() - 1; i >= 0; i--) {
    Operation& op = res_code[i];
    op.live_out_vars = live_vars;

    auto mark_var = [var_idxs, &live_vars](string name, bool mark) {
      // map<string, size_t> var_idxs;
      auto res_it = var_idxs.find(name);
      if (res_it != var_idxs.end())
        live_vars[res_it->second] = mark;
    };

    // -res, +left, +right
    mark_var(op.res_arg, false);
    mark_var(op.left_arg, true);
    mark_var(op.right_arg, true);

    op.live_in_vars = live_vars;
  }

  cout << endl << "printing live&dead vars..." << endl;
  PrintLiveVars(res_code, idx_to_var);
  cout << "finished" << endl << endl;

  Backend bcknd(var_addrs, idx_to_var);
  bcknd.GenerateCode(res_code);

  cout << endl << "final asm:" << endl;

  vector<string> res_asm = bcknd.GetResAsm();
  for (string& s : res_asm)
    cout << s << endl;

  return 0;
}
