TheJustMoose/74HCPU/soft/asm/assm.h

#pragma once

#include <bitset>
#include <cstdint>
#include <map>
#include <memory>
#include <optional>
#include <string>
#include <sstream>
#include <vector>

#include "ptr.h"
#include "../reg.h"
#include "slot_allocator.h"

// Code Of Operation
enum COP {
  cADD = 0x0000, cADDC = 0x1000,
  cAND = 0x2000, cOR = 0x3000, cXOR = 0x4000,
  cMUL = 0x5000, cUNO = 0x6000, cMOV = 0x7000,
  cLPM = 0x8000, cLPMW = 0x8100,
  cLD = 0x9000, cLDV = 0x9100,
  cIN = 0xA000, cOUT = 0xB000, cTOGL = 0xB004,
  cST = 0xC000, cSTV = 0xC100,
  cCMP = 0xD000, cCMPC = 0xE000,
  bCALL = 0xF000,
  bJMP = 0xF100,
  bRET = 0xF200,
  bRETI = 0xF300,
  bJL = 0xF400,
  bJE = 0xF500,
  bJNE = 0xF600,
  bJG = 0xF700,
  bJZ = 0xF800,
  bJNZ = 0xF900,
  bJC = 0xFA00,
  bJNC = 0xFB00,
  bJHC = 0xFC00,
  bJNHC = 0xFD00,
  bAFCALL = 0xFE00,
  bNOP = 0xFFFF,
  bSTOP = 0xFFFE,    // processor operation
  bERROR = 0x10000,  // we get some unknown name of operation
  cNO_OP = 0x20000   // just constant for "there is no operation here", for example for labels or error op names
};

const uint16_t cINV_LO = 0x0001;
const uint16_t cINV_HI = 0x0002;
const uint16_t cZERO_LO = 0x0004;
const uint16_t cZERO_HI = 0x0008;
const uint16_t cFORCE_CF = 0x0010;

enum OP_TYPE {
  tBINARY, tUNARY, tMEMORY, tIO, tBRANCH, tNO_OP
};

class Names {
 public:
  static COP CopFromName(std::string name);
  static REG RegFromName(std::string name);
  static PTR PtrFromName(std::string name, bool* inc, bool* dec);
  static int PortFromName(std::string name, std::string prefix);
};

class CodeGen {
 public:
  CodeGen(int line_number, COP cop)
   : line_number_(line_number), operation_(cop) {}
  virtual ~CodeGen() {}

  virtual uint16_t Emit() { return 0; }
  virtual void UpdateMachineCode(const std::map<std::string, uint16_t>& name_to_address) {}

  virtual std::vector<int> GetBlocks() { return {}; }
  virtual std::string cop() {
    std::stringstream s;
    s << std::bitset<16>(Emit());
    return s.str();
  }
  std::string FormattedCOP() {
    std::string res = cop();
    std::vector<int> blocks = GetBlocks();
    if (blocks.empty())
      return res;

    size_t pos {0};
    for (auto b : blocks) {
      pos += b;
      if (pos >= res.size())
        break;
      res.insert(pos, " ");
      pos++;
    }
    return res;
  }
  uint16_t Address() {
    return address_;
  }
  void SetAddress(uint16_t addr) {
    address_ = addr;
  }

  int LineNumber() {
    return line_number_;
  }

 protected:
  int line_number_ {0};
  uint16_t address_ {0};
  COP operation_ {cNO_OP};
};

class CodeLine {
 public:
  CodeLine(int line_number, std::string line_text);

  uint16_t GenerateMachineCode();
  void UpdateMachineCode(const std::map<std::string, uint16_t>& name_to_address);
  std::string FormattedCOP();

  std::vector<std::string> GetLabels() {
    return labels_;
  }

  bool HasLabels() {
    return labels_.size() > 0;
  }

  std::string GetLineText() {
    return line_text_;
  }

  std::optional<uint16_t> Address() {
    if (!code_gen_)
      return std::nullopt;
    return code_gen_->Address();
  }

  void SetAddress(uint16_t addr) {
    if (code_gen_)
      code_gen_->SetAddress(addr);
  }

  int LineNumber() {
    return line_number_;
  }

 private:
  int line_number_ {0};

  std::unique_ptr<CodeGen> code_gen_ {nullptr};

  std::vector<std::string> labels_ {};
  std::string line_text_ {};
};

class StringConst {
 public:
  StringConst() = default;
  StringConst(const std::string& str, int line_number): str_(str), line_number_(line_number) {}

  uint16_t GetSize() const;
  int LineNumber() const { return line_number_; }
  bool Address(uint16_t& address) const;
  void SetAddress(uint16_t);
  void PrintCode() const;
  void OutCode(std::vector<uint16_t>& code) const;
  std::string Str() const { return str_; }

 private:
  std::string str_ {};
  int line_number_ {0};
  std::optional<uint16_t> address_;
};

class DBConsts {
 public:
  DBConsts() = default;
  DBConsts(const std::vector<uint8_t>& data): data_(data) {}

  uint16_t GetSize() const;
  bool Address(uint16_t& address) const;
  void SetAddress(uint16_t address) { address_ = address; }
  void OutCode(std::vector<uint16_t>& code, bool verbose = false) const;

  std::string Join() const;

 private:
  std::vector<uint8_t> data_ {};
  std::optional<uint16_t> address_;
};

class DWConsts {
 public:
  struct Pair {
    std::string Name {};
    uint16_t Value {0};
  };

  DWConsts() = default;
  DWConsts(const std::vector<Pair>& data): data_(data) {}

  uint16_t GetSize() const;
  bool Address(uint16_t& address) const;
  void SetAddress(uint16_t address) { address_ = address; }
  void OutCode(std::vector<uint16_t>& code) const;

  std::string Join() const;

  void UpdateAddresses(const std::map<std::string, uint16_t>& new_addrs);

 private:
  std::vector<Pair> data_ {};
  std::optional<uint16_t> address_;
};

class Assembler {
 public:
  int Process(std::string fname, bool show_preprocess_out = false, bool verbose = false);
  int Process(std::map<int, std::string> lines, bool show_preprocess_out = false, bool verbose = false);
  void WriteBinary(std::string fname, bool strip_debug_info = false);

 protected:
  void PrintPreprocessed();
  void MergeCodeWithLabels();
  void ExtractOrgs();
  void ExtractStrings();
  void ExtractDBs();
  void ExtractDWs();

  void Pass1();  // generate machine code
  void Pass2();  // get real address of labels & string
  void Pass3();  // set real jump addresses

  void PrintCode();
  void OutCode(std::vector<uint16_t>& code, bool strip_debug_info = false);
  void OutDebugInfo(std::vector<uint16_t>& code);
  void PrintLabels();
  void PrintOrgs();
  void PrintStrings();
  void PrintDBs();
  void PrintDWs();

  template<typename T>
  void SetAddressesOf(std::map<std::string, T>& cont,
                      std::string cont_name, int max_line);

  bool IsOccupied(uint16_t addr) {
    return slot_allocator_.IsOccupied(addr);
  }

  void OccupyIt(uint16_t addr) {
    slot_allocator_.OccupyIt(addr);
  }

  bool OccupyIt(uint16_t addr, uint16_t size) {
    return slot_allocator_.OccupyIt(addr, size);
  }

  std::optional<uint16_t> GetFirstEmptyWindowWithSize(uint16_t size) {
    return slot_allocator_.GetFirstEmptyWindowWithSize(size);
  }

  uint16_t GetTotalSizeOfStringConsts() const;
  uint16_t GetTotalSizeOfDBConsts() const;
  uint16_t GetTotalSizeOfDWConsts() const;

 private:
  std::map<int, std::string> lines_ {};
  std::map<int, uint16_t> line_to_org_ {};
  std::vector<CodeLine> code_ {};
  // name_to_address_ contains labels and strings addresses:
  std::map<std::string, uint16_t> name_to_address_ {};

  SlotAllocator slot_allocator_;

  std::map<std::string, StringConst> string_consts_ {};
  std::map<std::string, DBConsts> db_consts_ {};
  std::map<std::string, DWConsts> dw_consts_ {};

  bool verbose_ {false};
};
