TheJustMoose/74HCPU/soft/expr/print_tree.cc

#include "print_tree.h"
#include "names.h"
#include "node.h"
#include "node_type.h"
#include "nodes.h"

#include <iostream>
#include <map>
#include <string>
#include <vector>

using namespace std;

const int kWidth = 80;

string dup(char c, int w) {
  string res(w, c);
  return res;
}

vector<Node*> gLinearTree;
map<const Node*, int> gNodeLevel;
map<const Node*, int> gNodeOffset;

void Tree2List(Node* n, int mid, int lvl = 0) {
  if (!n)
    return;
  gLinearTree.push_back(n);
  gNodeLevel[n] = lvl;
  gNodeOffset[n] = mid;
  //cout << "mid: " << mid << ", lvl: " << lvl << endl;

  if (BinOp* bop = dynamic_cast<BinOp*>(n)) {
    lvl++;
    int offset = kWidth / (lvl*2 + 5);
    Tree2List(bop->left.get(), mid - offset, lvl);
    Tree2List(bop->right.get(), mid + offset, lvl);
  } else if (RelationalOp* rop = dynamic_cast<RelationalOp*>(n)) {
    lvl++;
    int offset = kWidth / (lvl*2 + 5);
    Tree2List(rop->left.get(), mid - offset, lvl);
    Tree2List(rop->right.get(), mid + offset, lvl);
  } else if (AssignOp* aop = dynamic_cast<AssignOp*>(n)) {
    //cout << "assign..." << endl;
    lvl++;
    int offset = kWidth / (lvl*2 + 5);
    Tree2List(aop->left.get(), mid - offset, lvl);
    Tree2List(aop->right.get(), mid + offset, lvl);
  } else if (UnMinus* uop = dynamic_cast<UnMinus*>(n)) {
    //cout << "unary minus..." << endl;
    lvl++;
    Tree2List(uop->child.get(), mid, lvl);
  } else if (AddressOf* aof = dynamic_cast<AddressOf*>(n)) {
    lvl++;
    Tree2List(aof->child.get(), mid, lvl);
  } else if (DereferenceOp* dop = dynamic_cast<DereferenceOp*>(n)) {
    lvl++;
    Tree2List(dop->child.get(), mid, lvl);
  } else if (IncrementOp* iop = dynamic_cast<IncrementOp*>(n)) {
    lvl++;
    Tree2List(iop->child.get(), mid, lvl);
  } else if (IfStatement* ifop = dynamic_cast<IfStatement*>(n)) {
    lvl++;
    int offset = kWidth / (lvl*2 + 5);
    Tree2List(ifop->cond.get(), mid - offset, lvl);
    Tree2List(ifop->then_body.get(), mid + offset, lvl);
    Tree2List(ifop->else_body.get(), mid + offset, lvl);
  } else {
    //cout << "Node: " << GetNodeTypeName(n->node_type()) << endl;
  }
}

void TypeStringIntoTheBuffer(string& line, string word, int pos) {
  int left = pos - word.size() / 2;
  if (left < 0 || left >= line.size()) {
    cout << "Error! Word position is out of bounds!!" << endl;
    return;
  }

  for (size_t i = 0; i < word.size(); i++) {
    if (left + i >= line.size())
      break;
    line[left + i] = word[i];
  }
}

void PrintTree(Node* n) {
  if (!n)
    return;

  gLinearTree.clear();
  gNodeLevel.clear();
  gNodeOffset.clear();

  Tree2List(n, kWidth / 2);  // root node should be in a center of screen
  //cout << gLinearTree.size() << " items was stored" << endl;

  string line(kWidth, ' ');
  int last_lvl {0};
  int nodes_on_lvl {0};
  int cnt = 0;
  for (size_t i = 0; i < gLinearTree.size(); i++) {
    const Node* n = gLinearTree[i];
    int lvl = gNodeLevel[n];
    if (last_lvl != lvl) {
      cout << line << endl;

      line = string(kWidth, ' ');
      last_lvl = lvl;
      nodes_on_lvl = 1;  // we just found node on next level and node exist, so 'cnt' = 1
    } else {
      nodes_on_lvl++;
    }

    string name {"Oo"};
    if (const Name* name_node = dynamic_cast<const Name*>(n))
      name = name_node->name();

    if (const Num* num_node = dynamic_cast<const Num*>(n))
      name = to_string(num_node->value());

    if (const BinOp* binop_node = dynamic_cast<const BinOp*>(n))
      name = binop_node->name();

    if (const RelationalOp* rop_node = dynamic_cast<const RelationalOp*>(n))
      name = rop_node->name();

    if (const AssignOp* assop_node = dynamic_cast<const AssignOp*>(n))
      name = assop_node->op();

    if (const UnMinus* unminus_node = dynamic_cast<const UnMinus*>(n))
      name = unminus_node->name();

    if (const AddressOf* aof_node = dynamic_cast<const AddressOf*>(n))
      name = aof_node->name();

    if (const VarDecl* vard_node = dynamic_cast<const VarDecl*>(n))
      name = vard_node->var_names();

    if (const IfStatement* ifstmt_node = dynamic_cast<const IfStatement*>(n))
      name = ifstmt_node->name();

    TypeStringIntoTheBuffer(
        line,
        GetNodeTypeName(n->node_type()) + " (" + name + ")",  // to_string(gNodeOffset[n])
        gNodeOffset[n]);

    cnt++;
  }

  // Do not lose last iteration of loop!
  if (nodes_on_lvl > 0)
    cout << line << endl;

  cout << endl << dup('-', kWidth) << endl;
}
