TheJustMoose/74HCPU/soft/expr/lexer.cc

#include "lexer.h"
#include "names.h"

#include <cctype>
#include <iostream>
#include <map>

using namespace std;

map<string, Token> keywords {
  {"if", tIf},
  {"else", tElse},
};

// static
Lexer& Lexer::instance() {
  static Lexer lex;
  return lex;
}

void Lexer::consume() {
  findNextToken();
}

char Lexer::readChar() {
  return (idx_ < input_string_.size()) ? input_string_[idx_++] : 0;
}

void Lexer::findNextToken() {
  char c = readChar();
  if (isspace(c)) {     // if we have space, we have to skip it
    while (isspace(c))  // example: a b c
      c = readChar();
  }

  if (c == 0) {
    current_token_ = tEnd;
    return;
  }

  // Okay, now c != space
  if (isdigit(c)) {
    int value = 0;
    while (isdigit(c)) {
      int dig = c - '0';
      value = value*10 + dig;
      c = readChar();
    }
    if (c)
      idx_--;

    int_value_ = value;
    current_token_ = tNum;
    return;
  }

  if (isalpha(c) || c == '_') {
    string name;
    while (isalpha(c) || isdigit(c) || c == '_') {
      name += c;
      c = readChar();
    }
    if (c)
      idx_--;

    if (keywords.find(name) != keywords.end()) {
      current_token_ = keywords[name];
      return;
    }

    var_name_ = name;
    if (var_name_ == "int")
      current_token_ = tInt;
    else if (var_name_ == "byte")
      current_token_ = tByte;
    else if (var_name_ == "bool")
      current_token_ = tBool;
    else
      current_token_ = tName;
    return;
  }

  if (c == '+') {
    c = readChar();
    if (c == '+')
      current_token_ = tIncrement;
    else {
      current_token_ = tPlus;
      idx_--;
    }
    return;
  }

  if (c == '-') {
    c = readChar();
    if (c == '-')
      current_token_ = tDecrement;
    else {
      current_token_ = tMinus;
      idx_--;
    }
    return;
  }

  if (c == '<') {
    c = readChar();
    if (c == '=')
      current_token_ = tLessOrEqual;
    else {
      current_token_ = tLess;
      idx_--;
    }
    return;
  }

  if (c == '>') {
    c = readChar();
    if (c == '=')
      current_token_ = tGreaterOrEqual;
    else {
      current_token_ = tGreater;
      idx_--;
    }
    return;
  }

  if (c == '=') {
    c = readChar();
    if (c == '=')
      current_token_ = tEqual;
    else {
      current_token_ = tAssign;
      idx_--;
    }
    return;
  }

  if (c == '!') {
    c = readChar();
    if (c == '=')
      current_token_ = tNotEqual;
    else {
      current_token_ = tInversion;
      idx_--;
    }
    return;
  }

  switch (c) {
    case '*': current_token_ = tMul; return;
    case '/': current_token_ = tDiv; return;
    case '(': current_token_ = tLBracket; return;
    case ')': current_token_ = tRBracket; return;
    case ',': current_token_ = tComma; return;
    case ';': current_token_ = tSemicolon; return;
    case '@': current_token_ = tAtSign; return;
    case '#': current_token_ = tNumberSign; return;
    default: cout << "Lexer::findNextToken> Unknown token: "
                  << int(c) << endl; current_token_ = tError; break;
  }
}
