TheJustMoose/74HCPU/soft/expr/names.cc

#include "names.h"

#include <map>
#include <string>

using namespace std;

map<NodeType, string> NodeName {
  {ntName, "ntName"},
  {ntNum, "ntNum"},
  {ntSum, "ntSum"},
  {ntSub, "ntSub"},
  {ntMul, "ntMul"},
  {ntDiv, "ntDiv"},
  {ntUMinus, "ntUMinus"},
  {ntAssign, "ntAssign"},
  {ntAddressOf, "ntAddressOf"},
  {ntDereference, "ntDereference"},
  {ntIncrement, "ntIncrement"},
  {ntDecrement, "ntDecrement"},
  {ntLess, "ntLess"},
  {ntGreater, "ntGreater"},
  {ntLessOrEqual, "ntLessOrEqual"},
  {ntGreaterOrEqual, "ntGreaterOrEqual"},
  {ntIfStatement, "ntIfStatement"},
  {ntUnknown, "ntUnknown"},
  {ntVarDecl, "ntVarDecl"},
  {ntNull, "ntNull"},
};

map<Token, string> TokenName {
  {tPlus, "tPlus"},
  {tMinus, "tMinus"},
  {tMul, "tMul"},
  {tDiv, "tDiv"},
  {tNum, "tNum"},
  {tName, "tName"},
  {tComma, "tComma"},
  {tSemicolon, "tSemicolon"},
  {tAtSign, "tAtSign"},
  {tNumberSign, "tNumberSign"},
  {tLBracket, "tLBracket"},
  {tRBracket, "tRBracket"},
  {tAssign, "tAssign"},
  {tLess, "tLess"},
  {tGreater, "tGreater"},
  {tLessOrEqual, "tLessOrEqual"},
  {tGreaterOrEqual, "tGreaterOrEqual"},
  {tEqual, "tEqual"},
  {tNotEqual, "tNotEqual"},
  {tIncrement, "tIncrement"},
  {tDecrement, "tDecrement"},
  {tBool, "tBool"},
  {tByte, "tByte"},
  {tInt, "tInt"},
  {tInversion, "tInversion"},
  {tIf, "tIf"},
  {tElse, "tElse"},
  {tNone, "tNone"},
  {tError, "tError"},
  {tEnd, "tEnd"},
  {tNotInitialized, "tNotInitialized"},
};

string GetNodeTypeName(NodeType nt) {
  if (NodeName.find(nt) != NodeName.end())
    return NodeName[nt];
  else
    return "Unknown NodeType";
}

string GetTokenName(Token t) {
  if (TokenName.find(t) != TokenName.end())
    return TokenName[t];
  else
    return "Unknown Token";
}
