TheJustMoose/74HCPU/soft/expr/node_type.h

#pragma once

enum NodeType {
  // var   num    binary operations
  ntName, ntNum, ntSum, ntSub, ntMul, ntDiv,
  ntUMinus,      // unary minus
  ntAssign,      // a = b;
  ntAddressOf,   // #
  ntDereference, // @
  ntIncrement,   // ++
  ntDecrement,   // --
  ntLess,        // <
  ntGreater,     // >
  ntLessOrEqual, // <=
  ntGreaterOrEqual, // >=
  ntIfStatement, // just if
  ntUnknown,     // we do not know now what is it
  ntVarDecl,     // variable declaration node
  ntNull
};
