TheJustMoose/74HCPU/soft/expr/regs_bank.h

#pragma once

#include <cstdint>
#include <map>
#include <string>
#include <vector>

class ISpillable;

class RegsBank0 {
 public:
  const size_t RegCnt {8};
  const size_t npos {static_cast<size_t>(-1)};

  RegsBank0(ISpillable* p_spill,
            std::map<std::string, uint16_t> var_addrs,
            std::vector<std::string> res_asm)
    : p_spill_(p_spill), var_addrs_(var_addrs), res_asm_(res_asm) {}

  void Spill(size_t reg_idx);
  void Fill(std::string var_name, std::string reg_name);

  void FreeTheRegister(size_t reg_idx);

  std::string FindRegFor(std::string var_name);
  std::string DumpRegs();

  std::string operator[](size_t idx) {
    return bank0_[idx];
  }

  size_t GetIndexOfVar(std::string name);

 private:
  ISpillable* p_spill_ {nullptr};
  std::vector<std::string> bank0_ {RegCnt};
  std::map<std::string, uint16_t> var_addrs_;
  std::map<std::string, bool> var_was_spilled_;
  std::vector<std::string> res_asm_;
};
