TheJustMoose/74HCPU/soft/expr/lexer_unit_tests.cc

#define DOCTEST_CONFIG_IMPLEMENT_WITH_MAIN
#include <doctest.h>

#include "lexer.h"
#include "token.h"

#include <cctype>
#include <string>

using namespace std;

struct TestToken {
  Token token {tEnd};
  string text {""};
  int number {0};

  TestToken(Token t, string s, int i)
    : token(t), text(s), number(i) {}
};

void CheckLexerOutput(Lexer& l, const vector<TestToken>& right) {
  vector<TestToken> left;
  Token t {tEnd};
  do {
    t = l.currentToken();
    string s = l.getStrValue();
    int i = l.getIntValue();
    left.emplace_back(t, s, i);
    l.consume();
  } while (t != tEnd && t != tError);

  CHECK_EQ(left.size(), right.size());
  for (size_t i = 0; i < left.size(); i++) {
    CHECK_EQ(left[i].token, right[i].token);
    if (right[i].token == tName)
      CHECK_EQ(left[i].text, right[i].text);
    if (right[i].token == tNum)
      CHECK_EQ(left[i].number, right[i].number);
  }
}

TEST_CASE("check C++") {
  CHECK(isalpha('a'));
  CHECK(isalpha('Z'));

  CHECK( ! isalpha(' '));  // space is not isalpha
  CHECK_EQ(int(' '), 32);

  CHECK(isspace(' '));
  CHECK(isspace('\t'));
}

TEST_CASE("check Lexer") {
  Lexer l1("a");
  CHECK_EQ(l1.currentToken(), tName);
  CHECK_EQ(l1.getStrValue(), "a");

  Lexer l2("abcd");
  CHECK_EQ(l2.currentToken(), tName);
  CHECK_EQ(l2.getStrValue(), "abcd");

  Lexer l3("123");
  CHECK_EQ(l3.currentToken(), tNum);
  CHECK_EQ(l3.getIntValue(), 123);

  Lexer l4("1");
  CHECK_EQ(l4.currentToken(), tNum);
  CHECK_EQ(l4.getIntValue(), 1);

  Lexer l5("65535");
  CHECK_EQ(l5.currentToken(), tNum);
  CHECK_EQ(l5.getIntValue(), 65535);

  Lexer l6("if");
  CHECK_EQ(l6.currentToken(), tIf);
}

TEST_CASE("check Lexer tokens") {
  Lexer l("+");
  CHECK_EQ(l.currentToken(), tPlus);

  Lexer l12("++");
  CHECK_EQ(l12.currentToken(), tIncrement);

  Lexer l2("-");
  CHECK_EQ(l2.currentToken(), tMinus);

  Lexer l13("--");
  CHECK_EQ(l13.currentToken(), tDecrement);

  Lexer l3("*");
  CHECK_EQ(l3.currentToken(), tMul);

  Lexer l4("/");
  CHECK_EQ(l4.currentToken(), tDiv);

  Lexer l5("(");
  CHECK_EQ(l5.currentToken(), tLBracket);

  Lexer l6(")");
  CHECK_EQ(l6.currentToken(), tRBracket);

  Lexer l7("=");
  CHECK_EQ(l7.currentToken(), tAssign);

  Lexer l8(";");
  CHECK_EQ(l8.currentToken(), tSemicolon);

  Lexer l9("@");
  CHECK_EQ(l9.currentToken(), tAtSign);

  Lexer l10("#");
  CHECK_EQ(l10.currentToken(), tNumberSign);

  Lexer l11("$");
  CHECK_EQ(l11.currentToken(), tError);

  Lexer l14("==");
  CHECK_EQ(l14.currentToken(), tEqual);

  Lexer l15("<=");
  CHECK_EQ(l15.currentToken(), tLessOrEqual);

  Lexer l16(">=");
  CHECK_EQ(l16.currentToken(), tGreaterOrEqual);

  Lexer l17("!=");
  CHECK_EQ(l17.currentToken(), tNotEqual);

  Lexer l18("!");
  CHECK_EQ(l18.currentToken(), tInversion);

  Lexer l19("<");
  CHECK_EQ(l19.currentToken(), tLess);

  Lexer l20(">");
  CHECK_EQ(l20.currentToken(), tGreater);
}

TEST_CASE("check Lexer and many long strings") {
  Lexer l("abcd efgh");

  vector<TestToken> r {
    {tName, "abcd", 0},
    {tName, "efgh", 0},
    {tEnd, "", 0},
  };

  CheckLexerOutput(l, r);
}

TEST_CASE("check Lexer and many numbers") {
  Lexer l("12 234 56789");

  vector<TestToken> r {
    {tNum, "", 12},
    {tNum, "", 234},
    {tNum, "", 56789},
    {tEnd, "", 0},
  };

  CheckLexerOutput(l, r);
}

TEST_CASE("check Lexer and numbers and string") {
  Lexer l("12 234 abc");

  vector<TestToken> r {
    {tNum, "", 12},
    {tNum, "", 234},
    {tName, "abc", 0},
    {tEnd, "", 0},
  };

  CheckLexerOutput(l, r);
}

TEST_CASE("check Lexer: Okay, now we can check arithm") {
  Lexer l("12+234-56");

  vector<TestToken> r {
    {tNum, "", 12},
    {tPlus, "", 0},
    {tNum, "", 234},
    {tMinus, "", 0},
    {tNum, "", 56},
    {tEnd, "", 0},
  };

  CheckLexerOutput(l, r);
}

TEST_CASE("check Lexer with sum") {
  Lexer l("1+1;");

  vector<TestToken> r {
    {tNum, "", 1},
    {tPlus, "", 0},
    {tNum, "", 1},
    {tSemicolon, "", 0},
    {tEnd, "", 0},
  };

  CheckLexerOutput(l, r);
}

TEST_CASE("check Lexer last token") {
  Lexer l("int a = 2; a = 0;");

  CHECK_EQ(l.currentToken(), tInt);
  l.consume();
  CHECK_EQ(l.currentToken(), tName);
  l.consume();
  CHECK_EQ(l.currentToken(), tAssign);
  l.consume();
  CHECK_EQ(l.currentToken(), tNum);
  l.consume();
  CHECK_EQ(l.currentToken(), tSemicolon);
  l.consume();

  CHECK_EQ(l.currentToken(), tName);
  l.consume();
  CHECK_EQ(l.currentToken(), tAssign);
  l.consume();
  CHECK_EQ(l.currentToken(), tNum);
  l.consume();
  CHECK_EQ(l.currentToken(), tSemicolon);
  l.consume();

  CHECK_EQ(l.currentToken(), tEnd);
  l.consume();
}
